ANToNyS21/DMP2025/prubezna kontrola/photos.docx

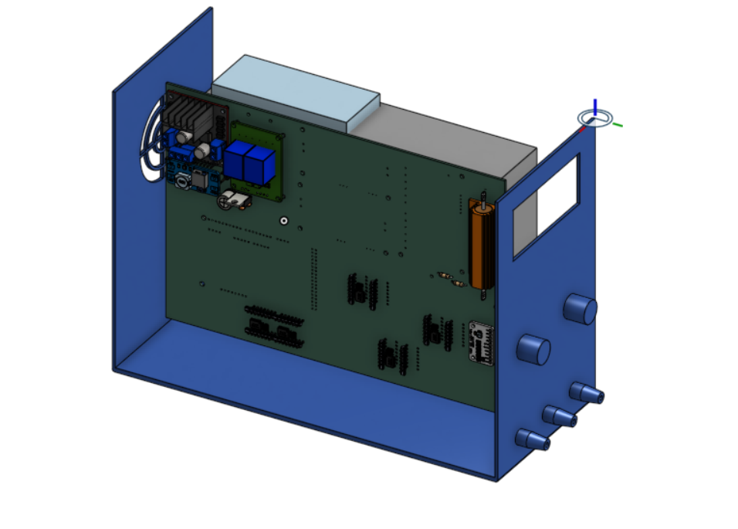
[picture p44: figure]
Obsah obrázku stroj/přístroj Popis byl vytvořen automaticky
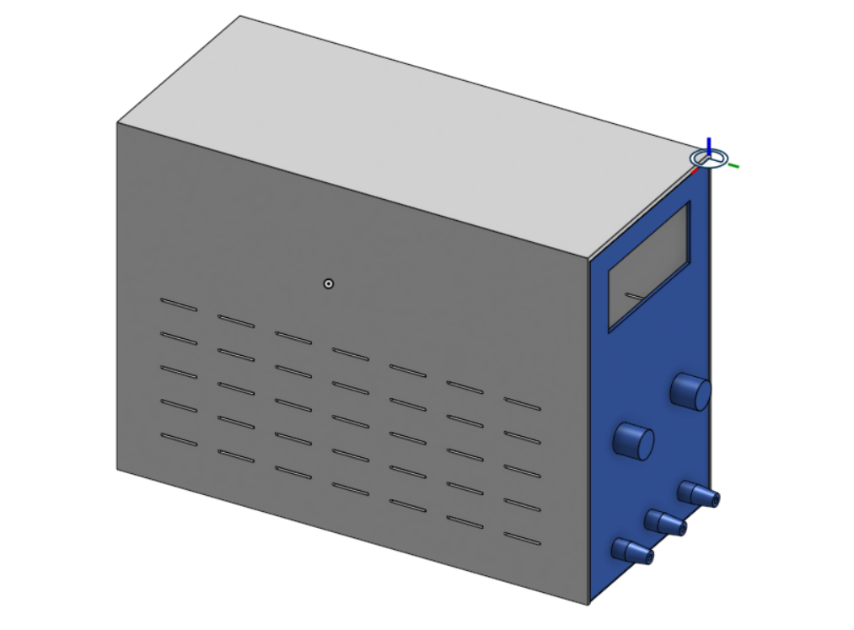
[picture p45: figure]
Obsah obrázku design Popis byl vytvořen automaticky
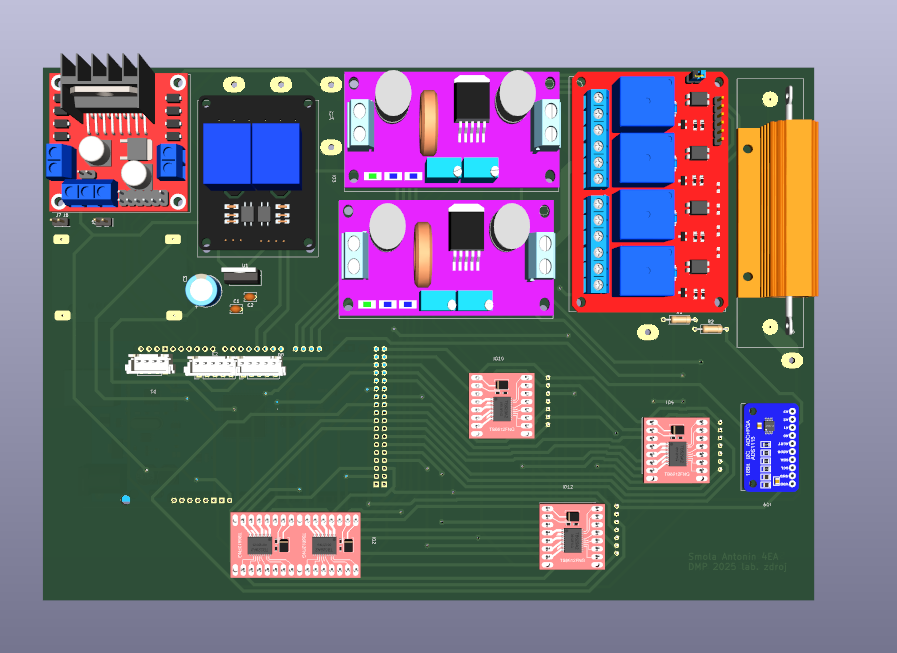
[picture p46: figure]
Obsah obrázku text, snímek obrazovky, Obdélník, Plán Popis byl vytvořen automaticky
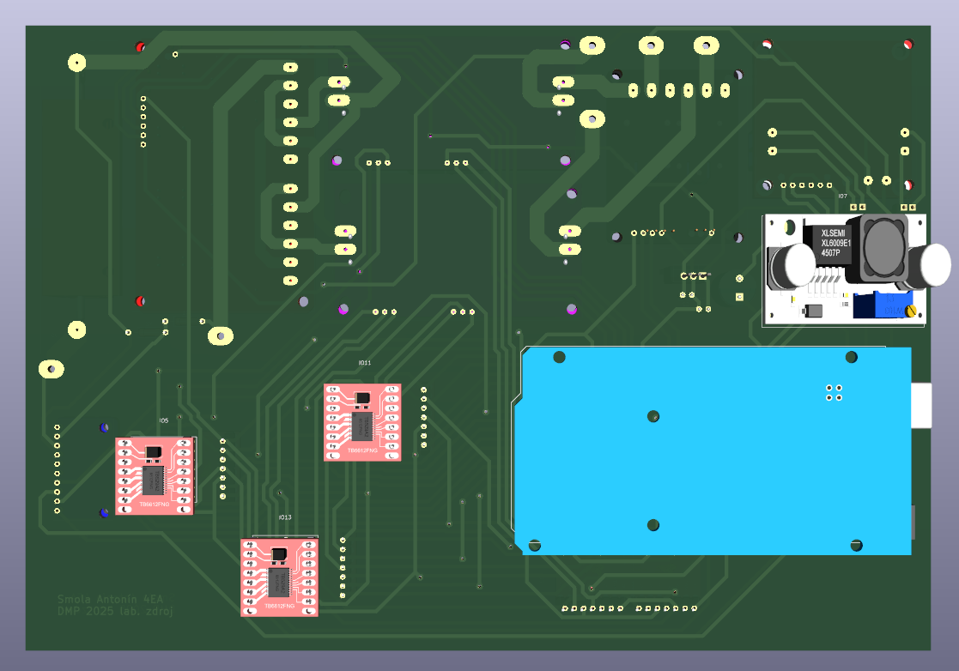
[picture p47: figure]
Obsah obrázku text, obvod, mapa, snímek obrazovky Popis byl vytvořen automaticky
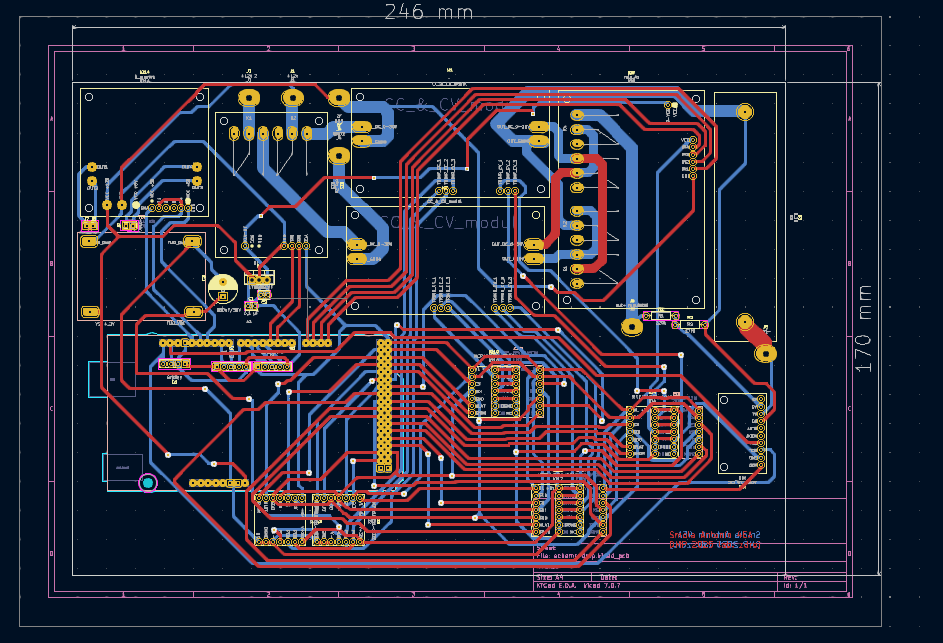
[picture p48: figure]
Obsah obrázku text, snímek obrazovky, obvod, mapa Popis byl vytvořen automaticky
