ANToNyS21/DMP2025/prubezna kontrola/prubezna prezentace.pptx

## Laboratorní zdroj

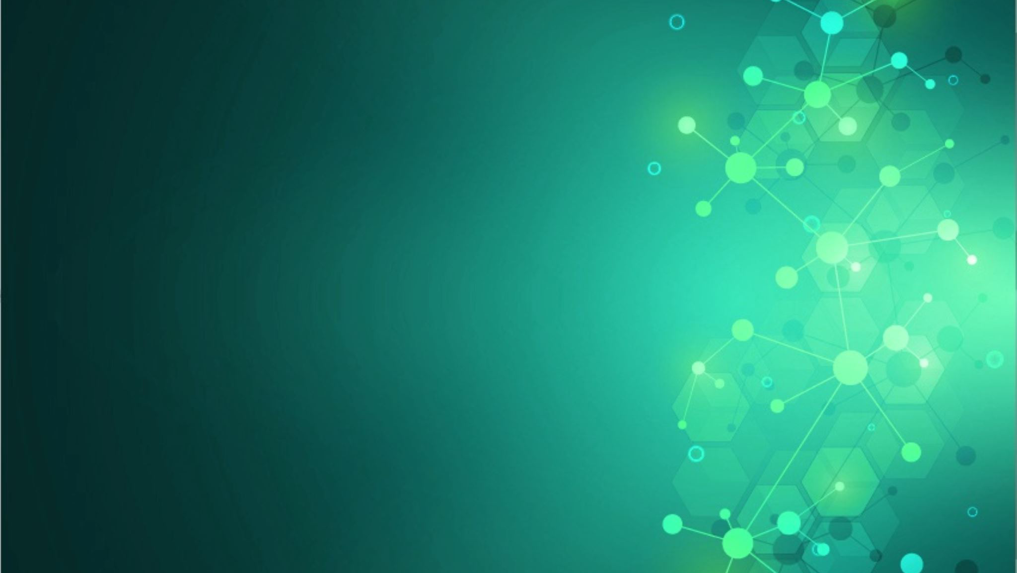
[picture p49: figure]
Obsah obrázku snímek obrazovky, voda, Tyrkysový, zelené Popis byl vytvořen automaticky

Smola Antonín 4EA
Vedoucí : Jan Kárník
05.11.2024

## Řešená témata:

Motivace
Problémy
Řešení
Momentální fáze

## Motivace

- Doplnění stávajícího analogového Laboratorního zdroje o digitální variantu
- Potřeba Laboratorního zdroje s enkoderem

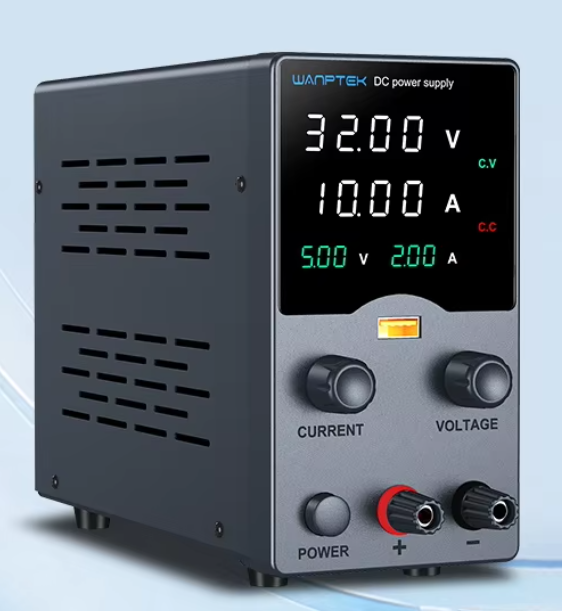
[picture p50: figure]

## Zakoupeno

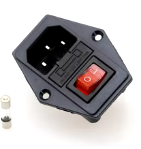
[picture p51: figure]
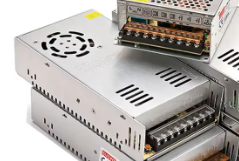
[picture p52: figure]
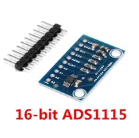
[picture p53: figure]
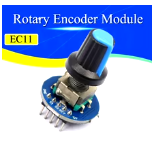
[picture p54: figure]
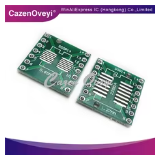
[picture p55: figure]
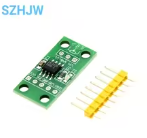
[picture p56: figure]
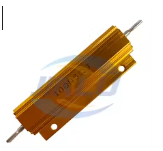
[picture p57: figure]
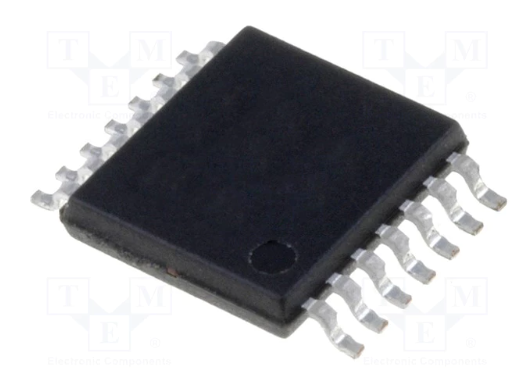
[picture p58: figure]
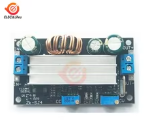
[picture p59: figure]

## Uděláno

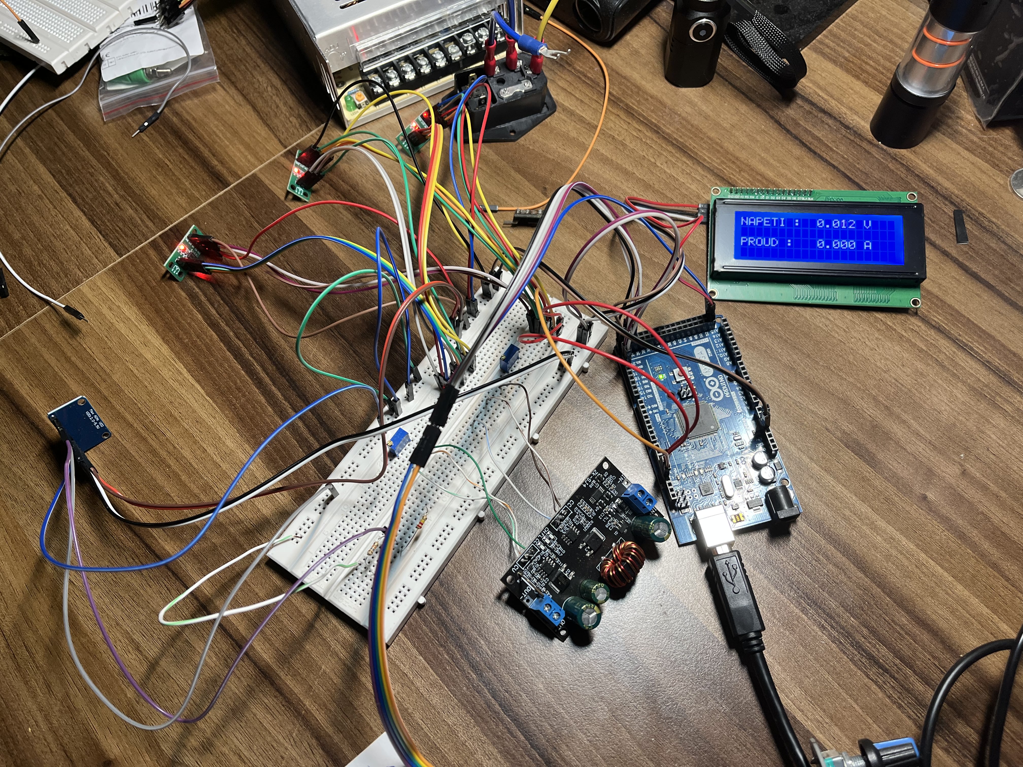
[picture p60: figure]
Obsah obrázku elektronika, Elektronické inženýrství, Elektrické vedení, kabel Popis byl vytvořen automaticky

## Uděláno

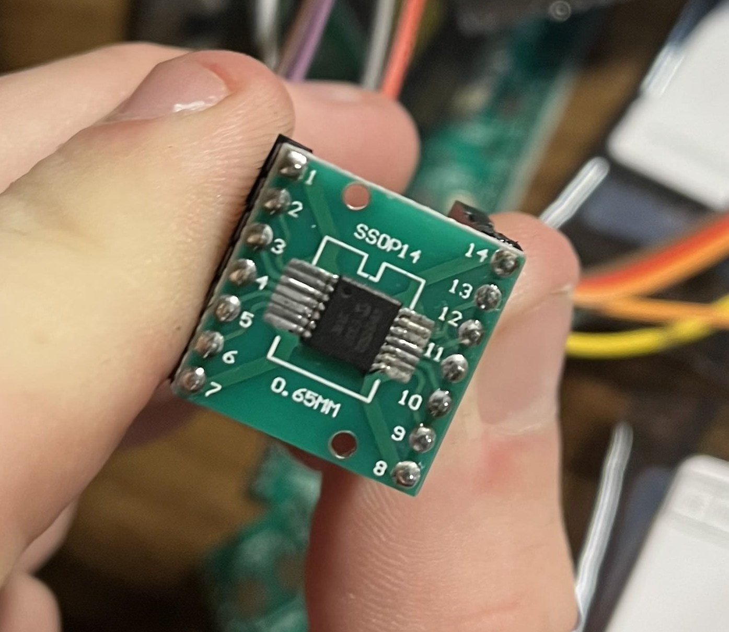
[picture p61: figure]
Obsah obrázku Elektronické inženýrství, Elektronická součástka, Obvodoví součástka, obvod Popis byl vytvořen automaticky

## Uděláno

- Videa:

## Konec Laboratorní zdroj

Smola Antonín 4EA
Vedoucí : Jan Kárník
05.11.2024
