ANToNyS21/DMP2025/prubezna kontrola/DMP_ELEKTRO.drawio.png

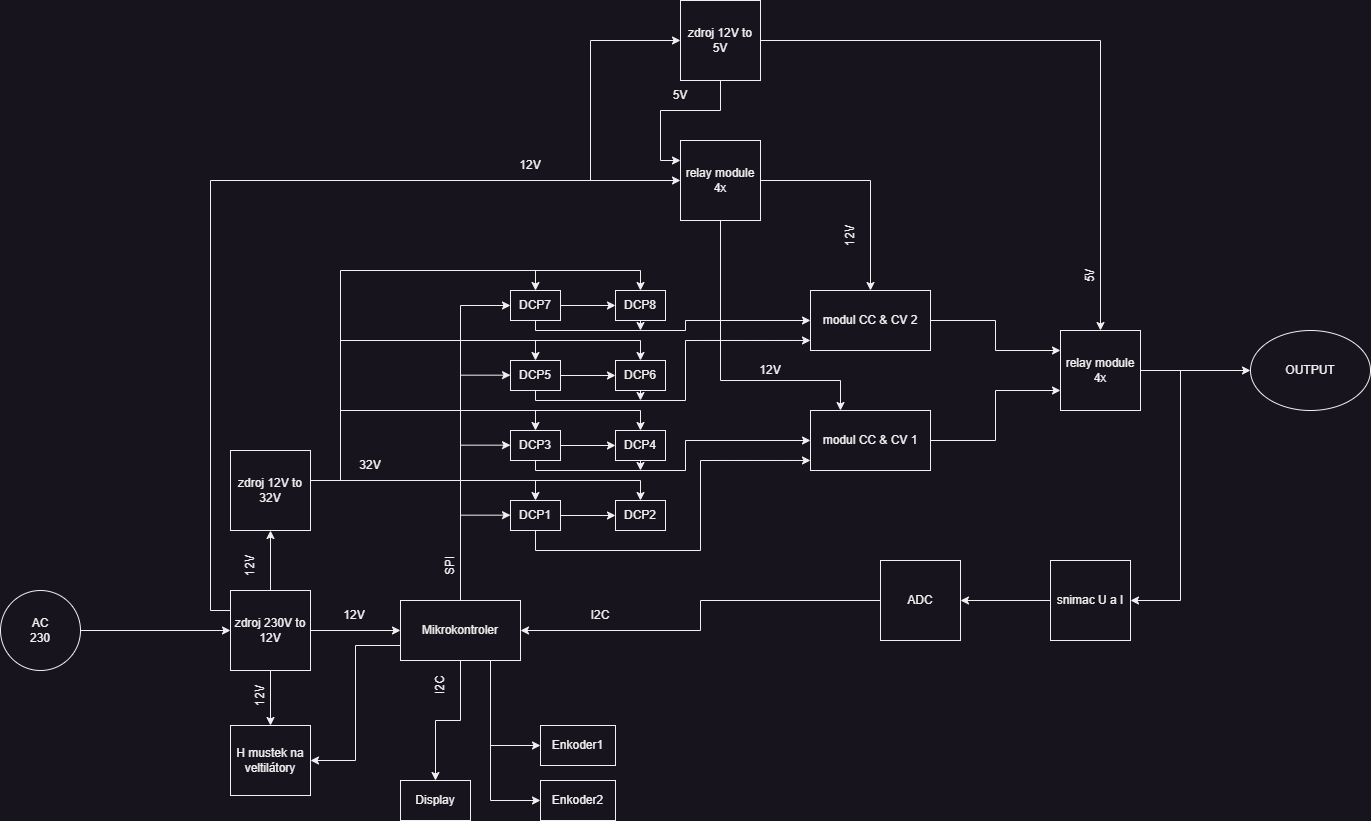
prubezna kontrola/DMP_ELEKTRO.drawio.png
