ANToNyS21/DMP2025/prubezna kontrola/program/prubezny diagram.png

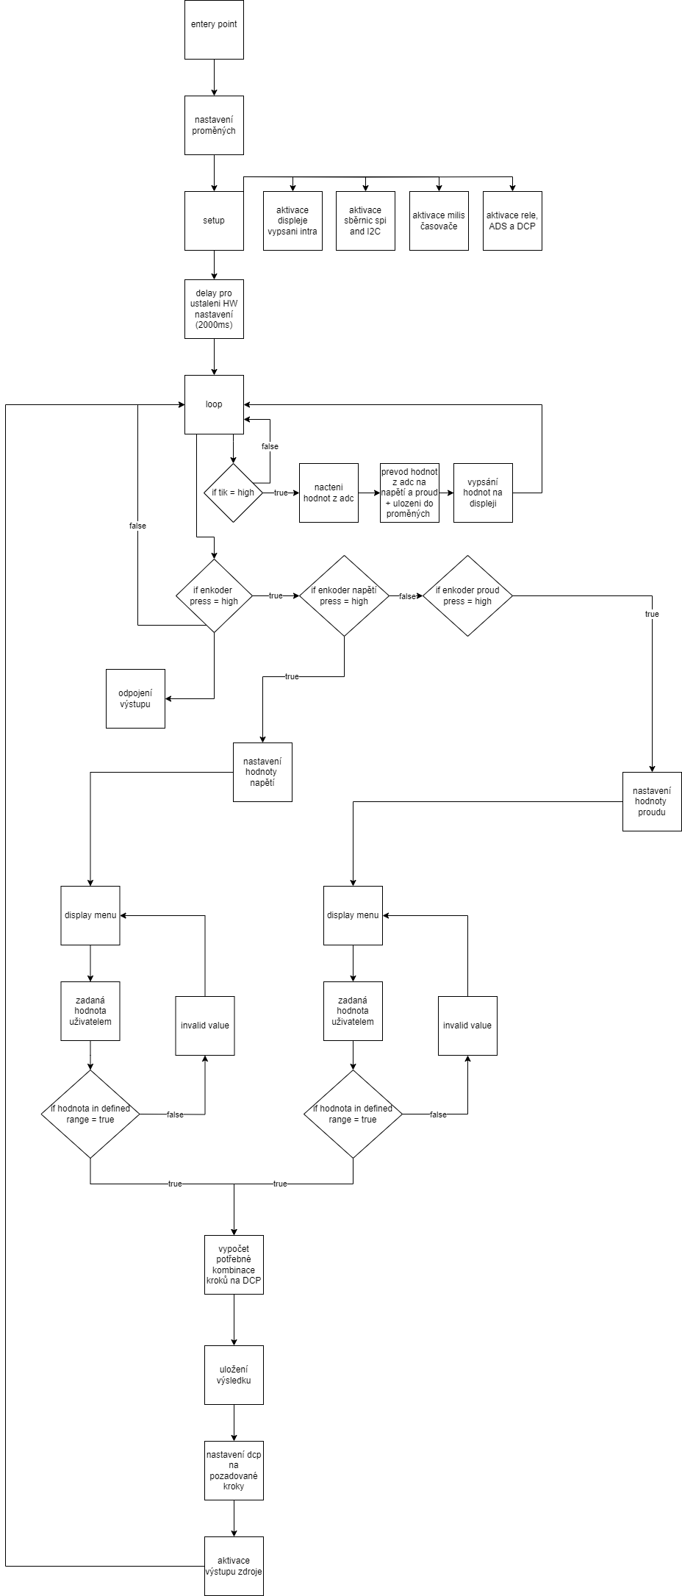
prubezna kontrola/program/prubezny diagram.png
