ANToNyS21/DMP2025/smolaan21/elektrika/board layout2.png

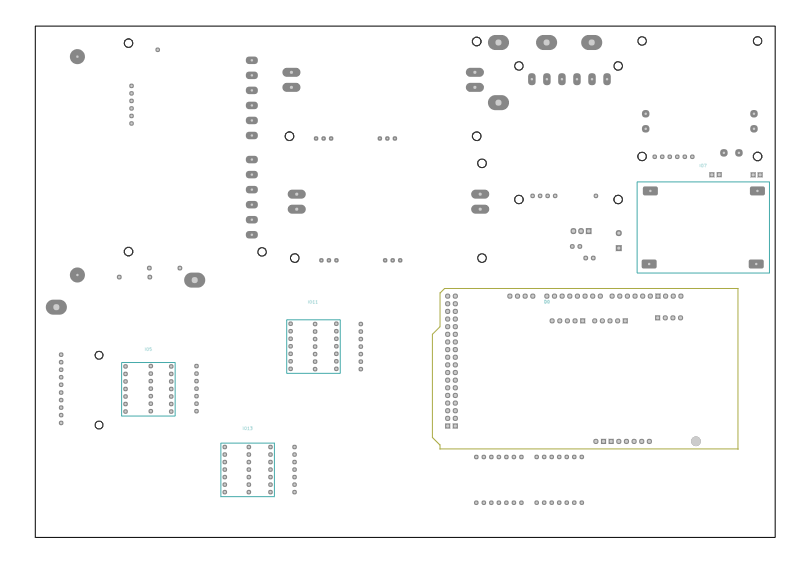
smolaan21/elektrika/board layout2.png
