ANToNyS21/DMP2025/smolaan21/elektrika/board layout.png

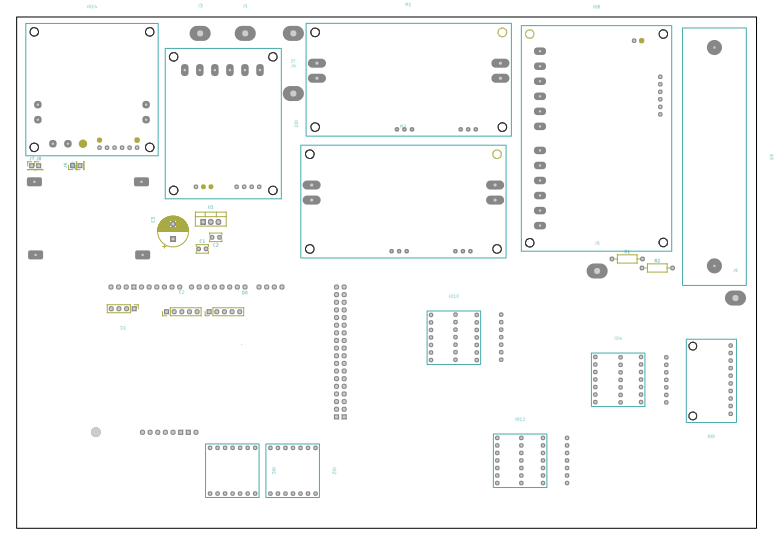
smolaan21/elektrika/board layout.png
