ANToNyS21/DMP2025/smolaan21/media/DCP_na_SMD_break_out.JPG

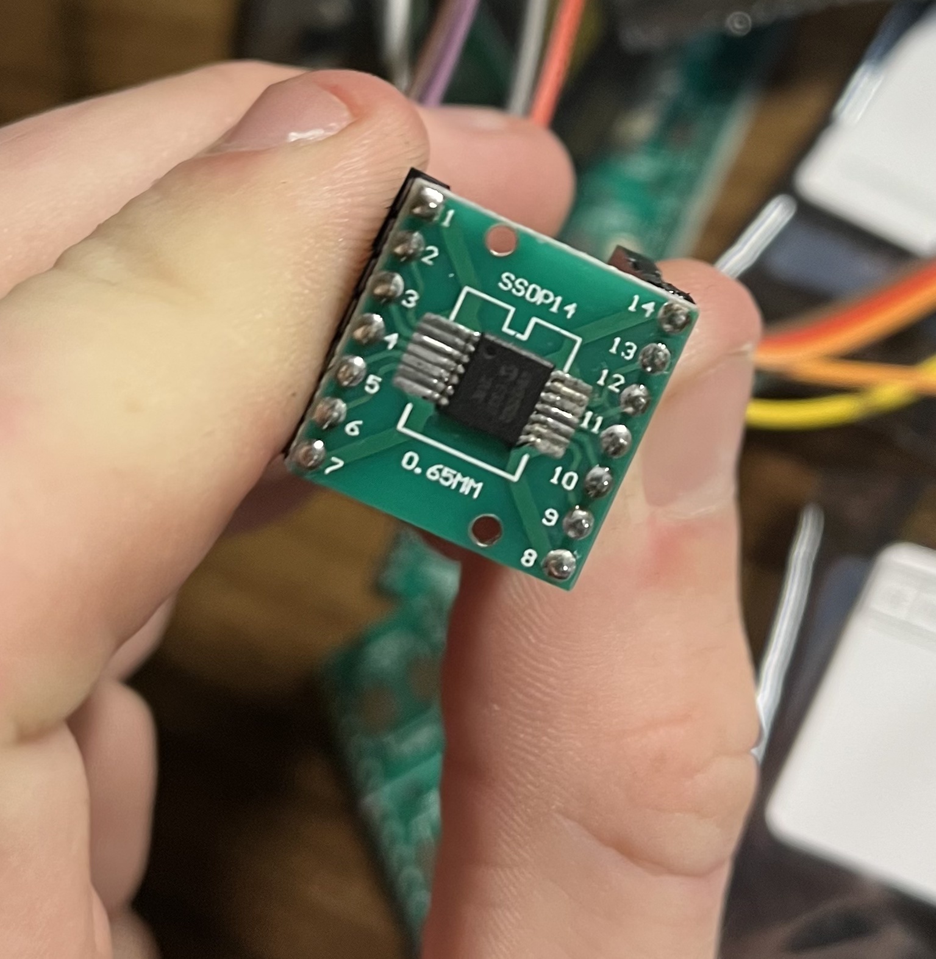
smolaan21/media/DCP_na_SMD_break_out.JPG
