ANToNyS21/DMP2025/smolaan21/media/DPS_s_arduinem.JPG

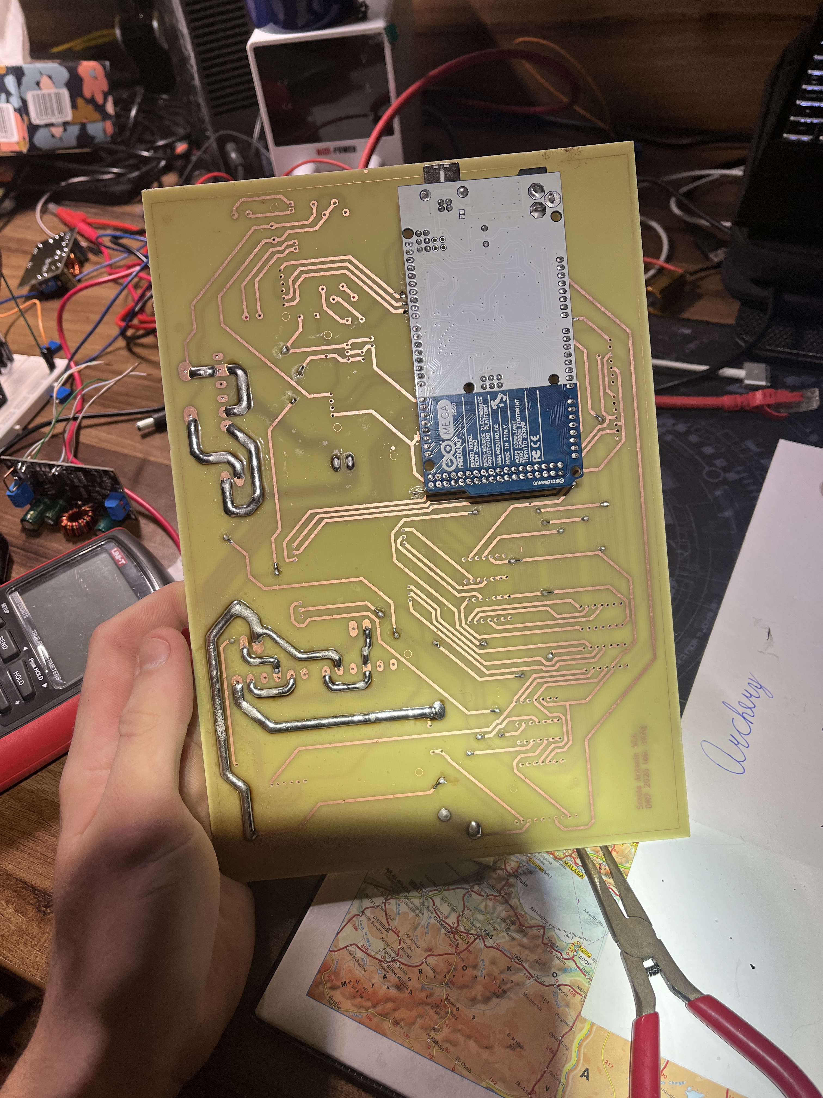
smolaan21/media/DPS_s_arduinem.JPG
