ANToNyS21/DMP2025/smolaan21/media/DPS_se_zesílenými_cestami.JPG

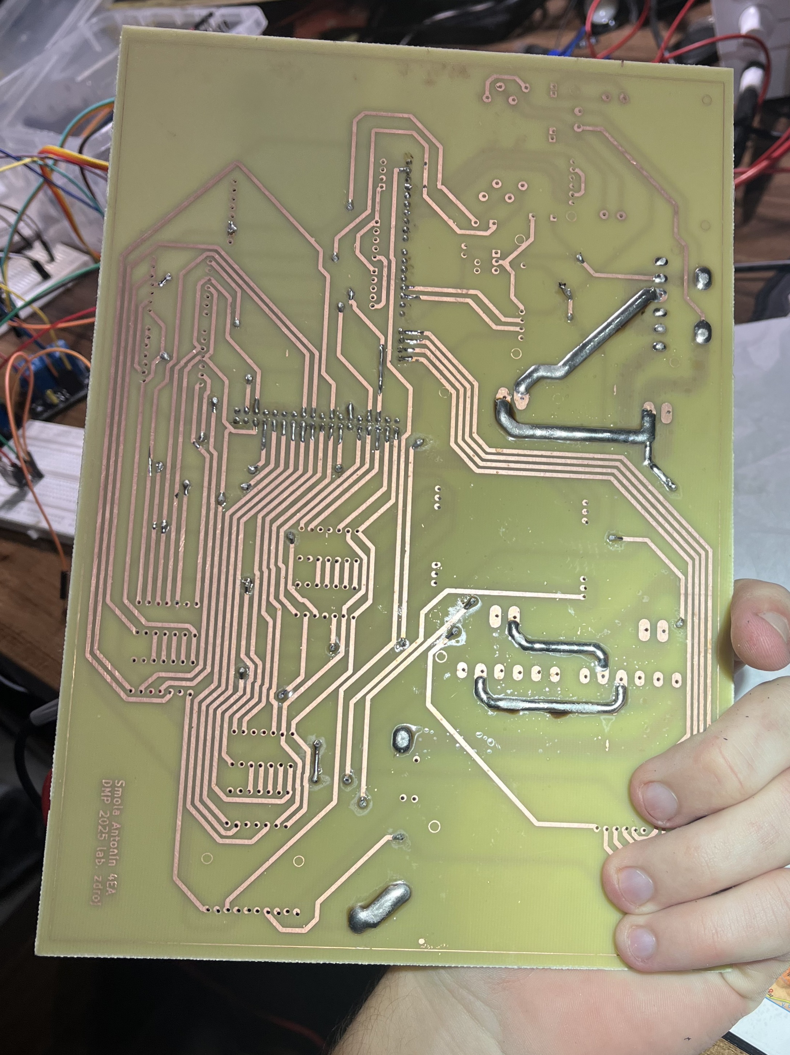
smolaan21/media/DPS_se_zesílenými_cestami.JPG
