ANToNyS21/DMP2025/smolaan21/media/finalně_osazená_DPS_B.jpg

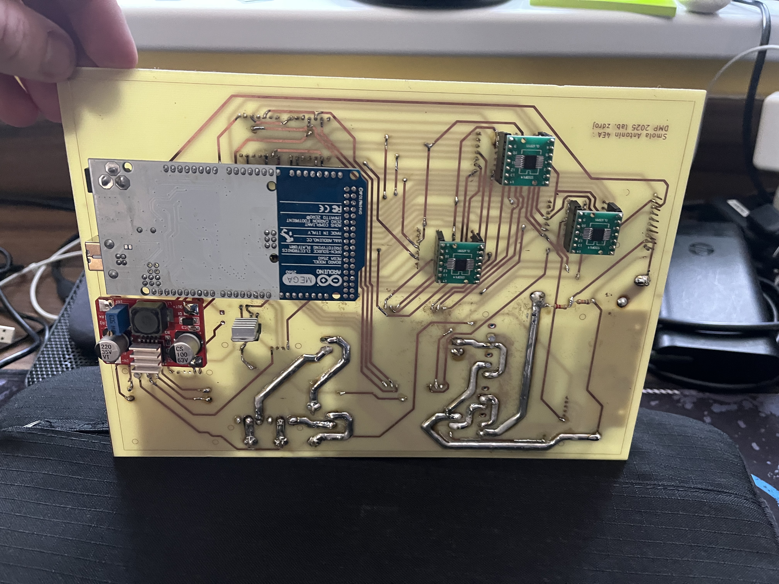
smolaan21/media/finalně_osazená_DPS_B.jpg
