ANToNyS21/DMP2025/smolaan21/media/finalně_osazená_DPS_F.jpg

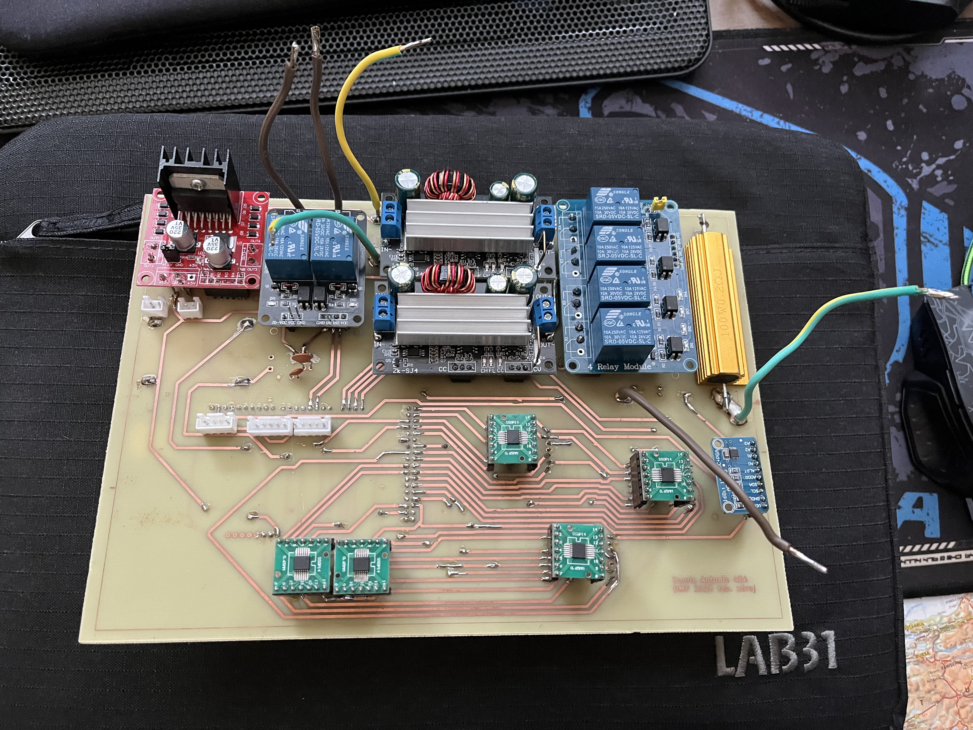
smolaan21/media/finalně_osazená_DPS_F.jpg
