ANToNyS21/DMP2025/smolaan21/media/finálně_osazená_schránka1.jpeg

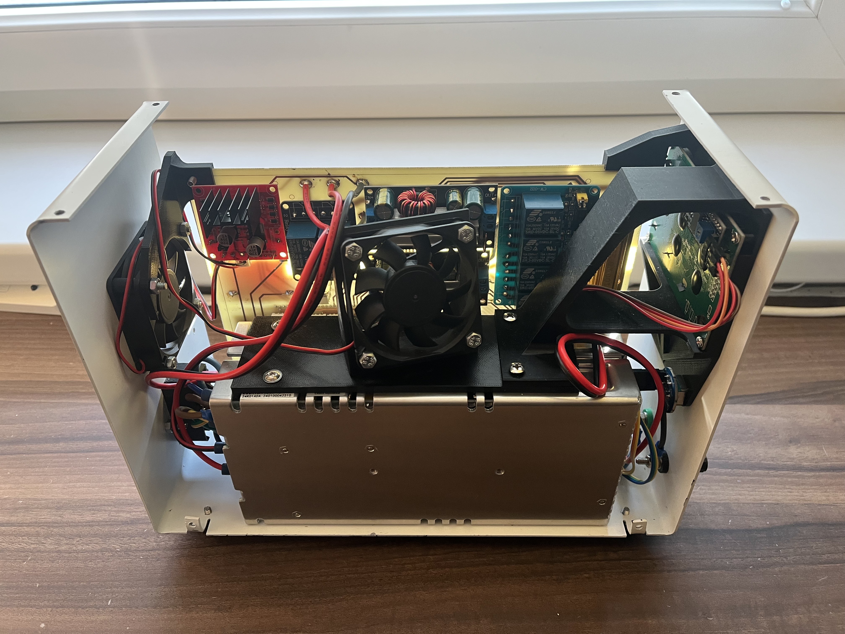
smolaan21/media/finálně_osazená_schránka1.jpeg
