ANToNyS21/DMP2025/smolaan21/media/nanesený_lak.jpeg

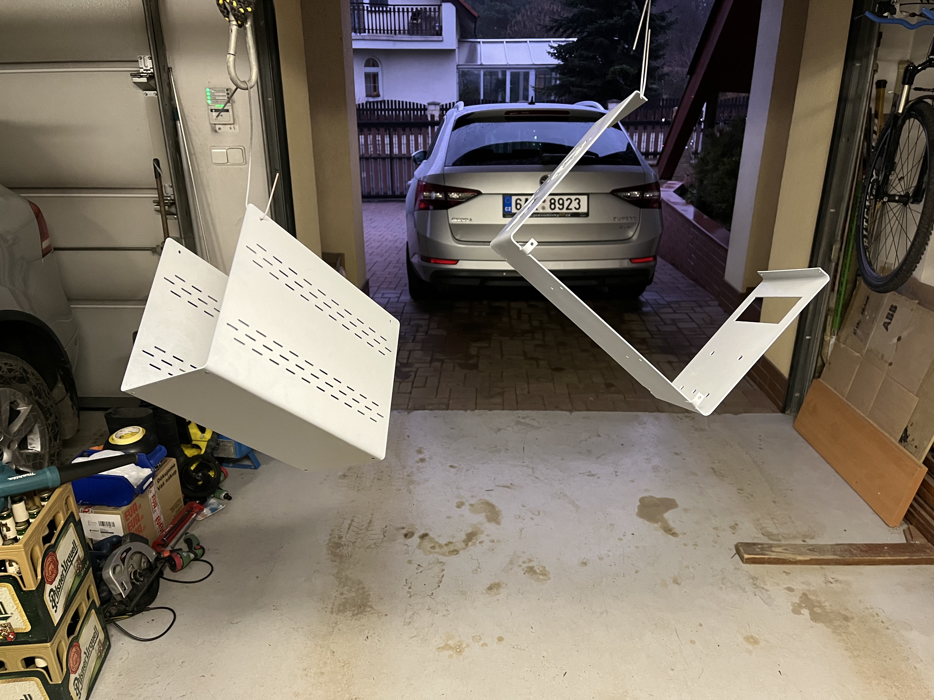
smolaan21/media/nanesený_lak.jpeg
