ANToNyS21/DMP2025/smolaan21/media/nanesený_plnič.jpeg

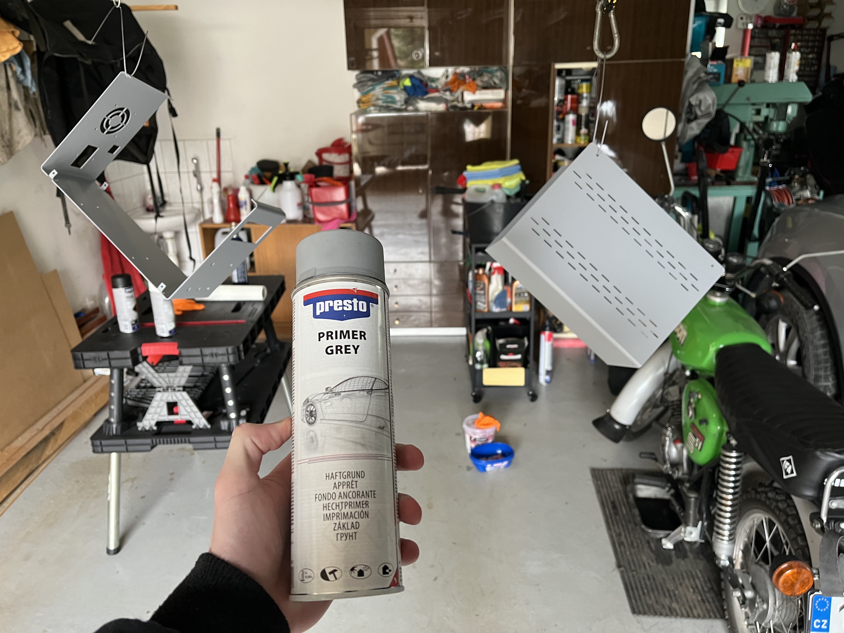
smolaan21/media/nanesený_plnič.jpeg
