ANToNyS21/DMP2025/smolaan21/media/naohýbaná_schránka2.jpeg

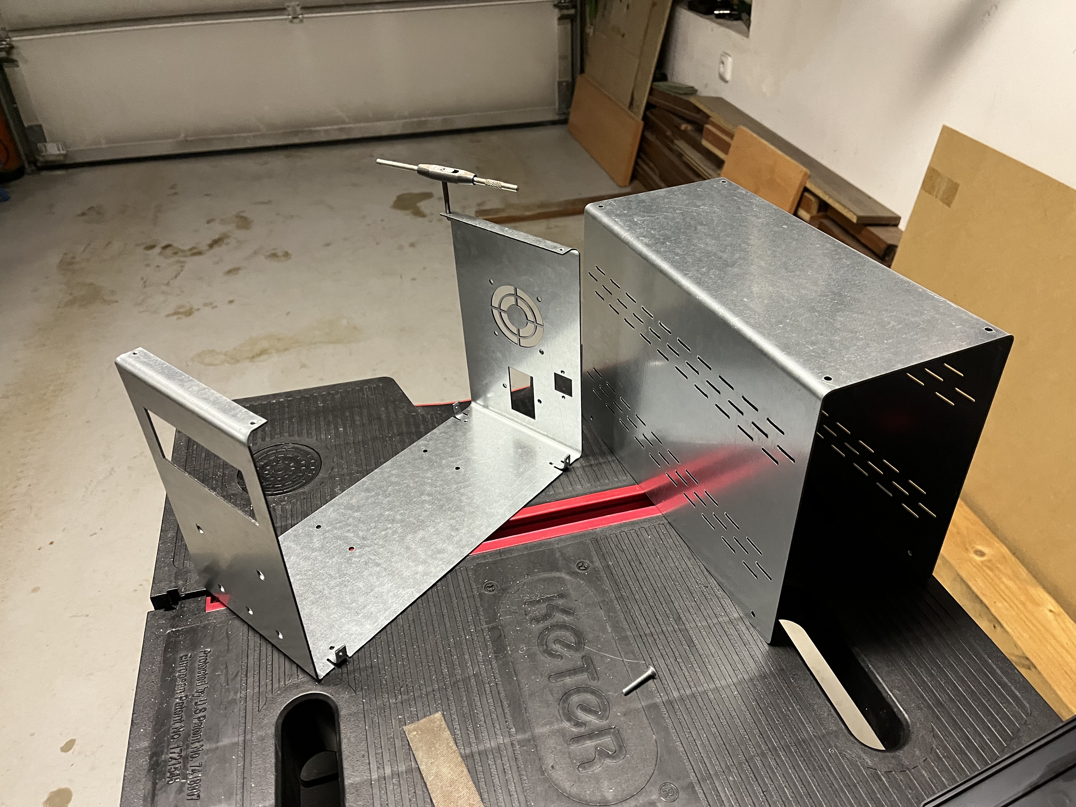
smolaan21/media/naohýbaná_schránka2.jpeg
