ANToNyS21/DMP2025/smolaan21/media/naohýbaná_schránka4.jpeg

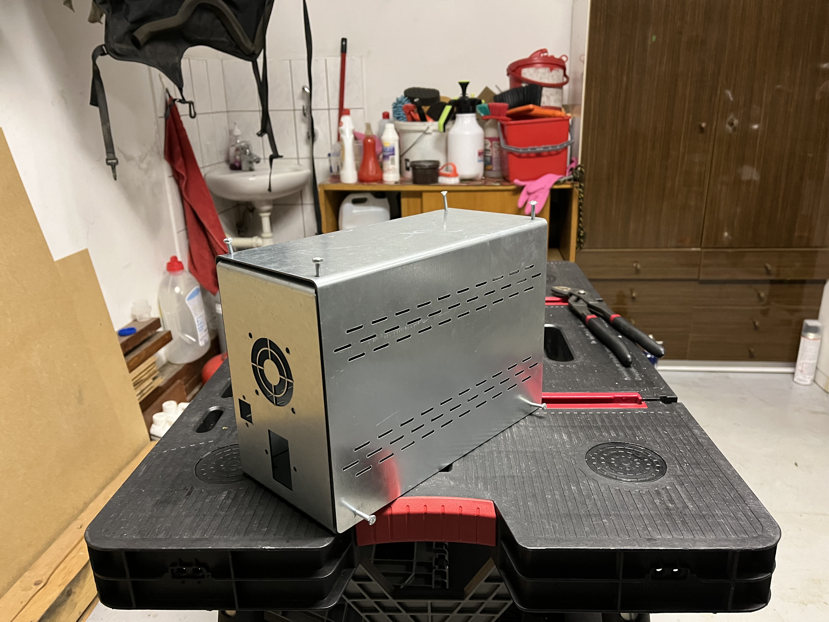
smolaan21/media/naohýbaná_schránka4.jpeg
