ANToNyS21/DMP2025/smolaan21/media/připojené_konektory_UI.jpg

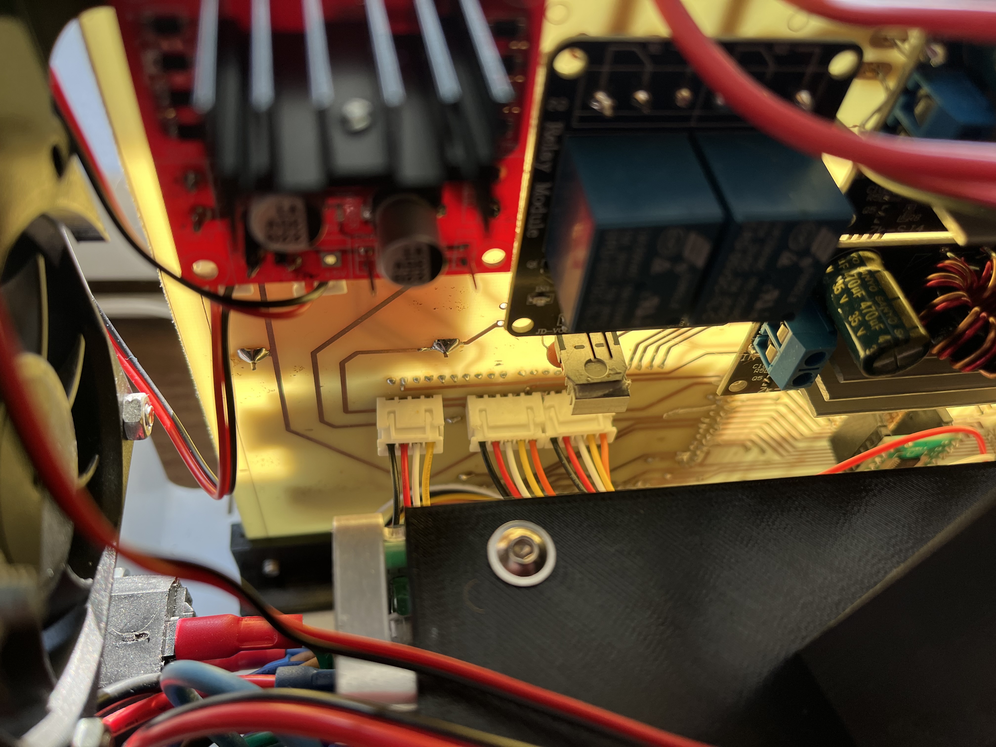
smolaan21/media/připojené_konektory_UI.jpg
