ANToNyS21/DMP2025/smolaan21/media/zakrytovaný_laboratorní_zdroj_s_polepy_2.jpg

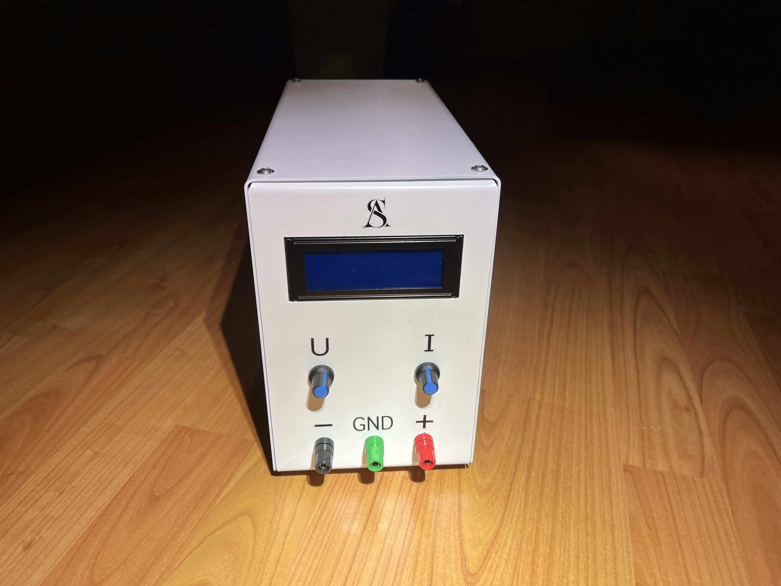
smolaan21/media/zakrytovaný_laboratorní_zdroj_s_polepy_2.jpg
