ANToNyS21/DMP2025/smolaan21/media/školní_leptací_stanice.jpg

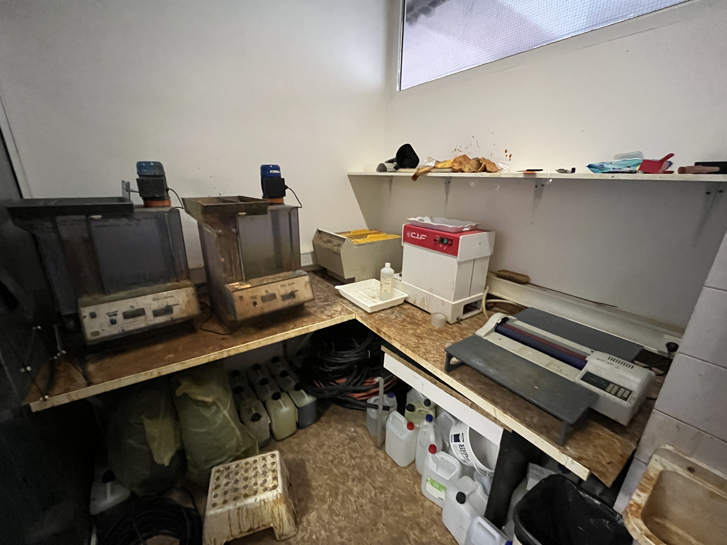
smolaan21/media/školní_leptací_stanice.jpg
