ANToNyS21/DMP2025/knihovna_kicad/Smola_dmp/100W 30OHM RESISTOR.STEP

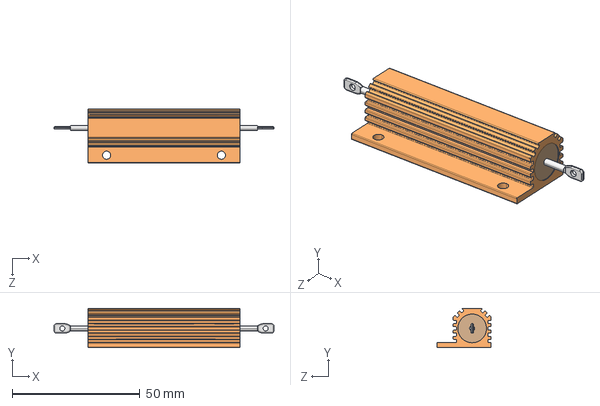
[picture p102: CAD file, 2025-02-05]
knihovna_kicad/Smola_dmp/100W 30OHM RESISTOR.STEP
86.2 x 15.4 x 21.2 mm
