ANToNyS21/DMP2025/smolaan21/mechanika/sheetmetal 1.5mm - programing port cap.step

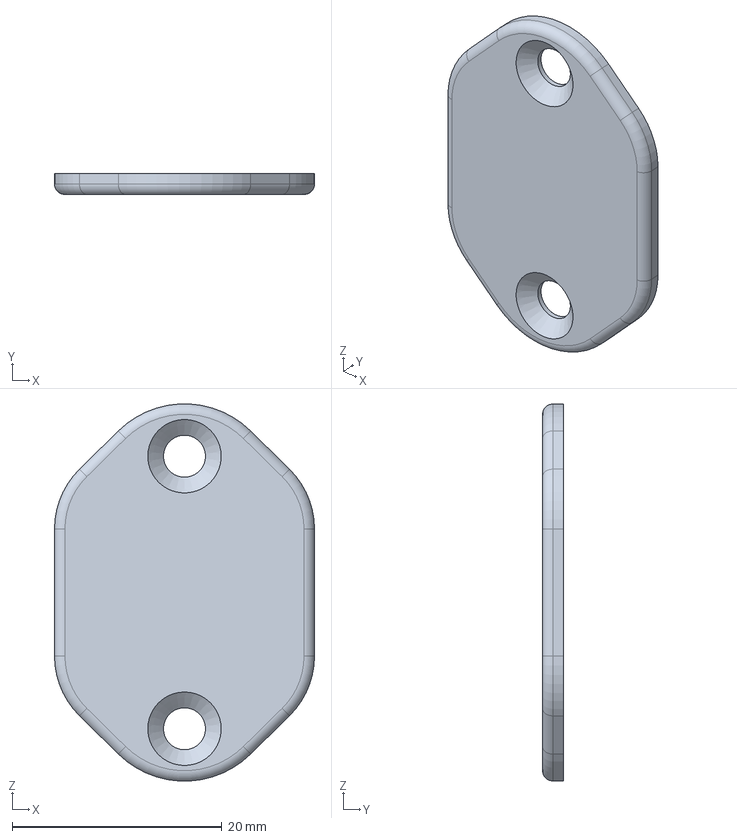
[picture p103: CAD file, 2025-02-25]
smolaan21/mechanika/sheetmetal 1.5mm - programing port cap.step
24.8 x 2.00 x 36.0 mm
