ANToNyS21/DMP2025/smolaan21/mechanika/stencil_front.step

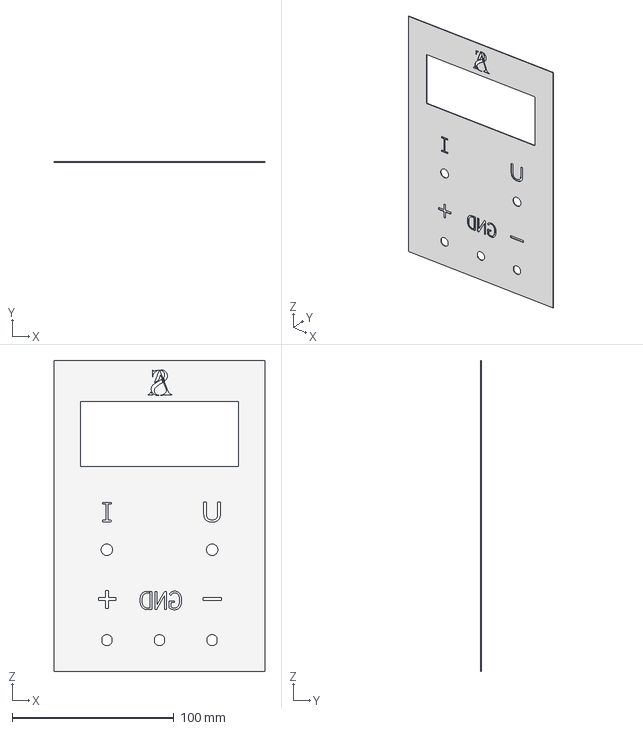
[picture p104: CAD file, 2025-02-25]
smolaan21/mechanika/stencil_front.step
130.0 x 0.5 x 192.0 mm
