ANToNyS21/DMP2025/schema dmp/schema dmp.pdf

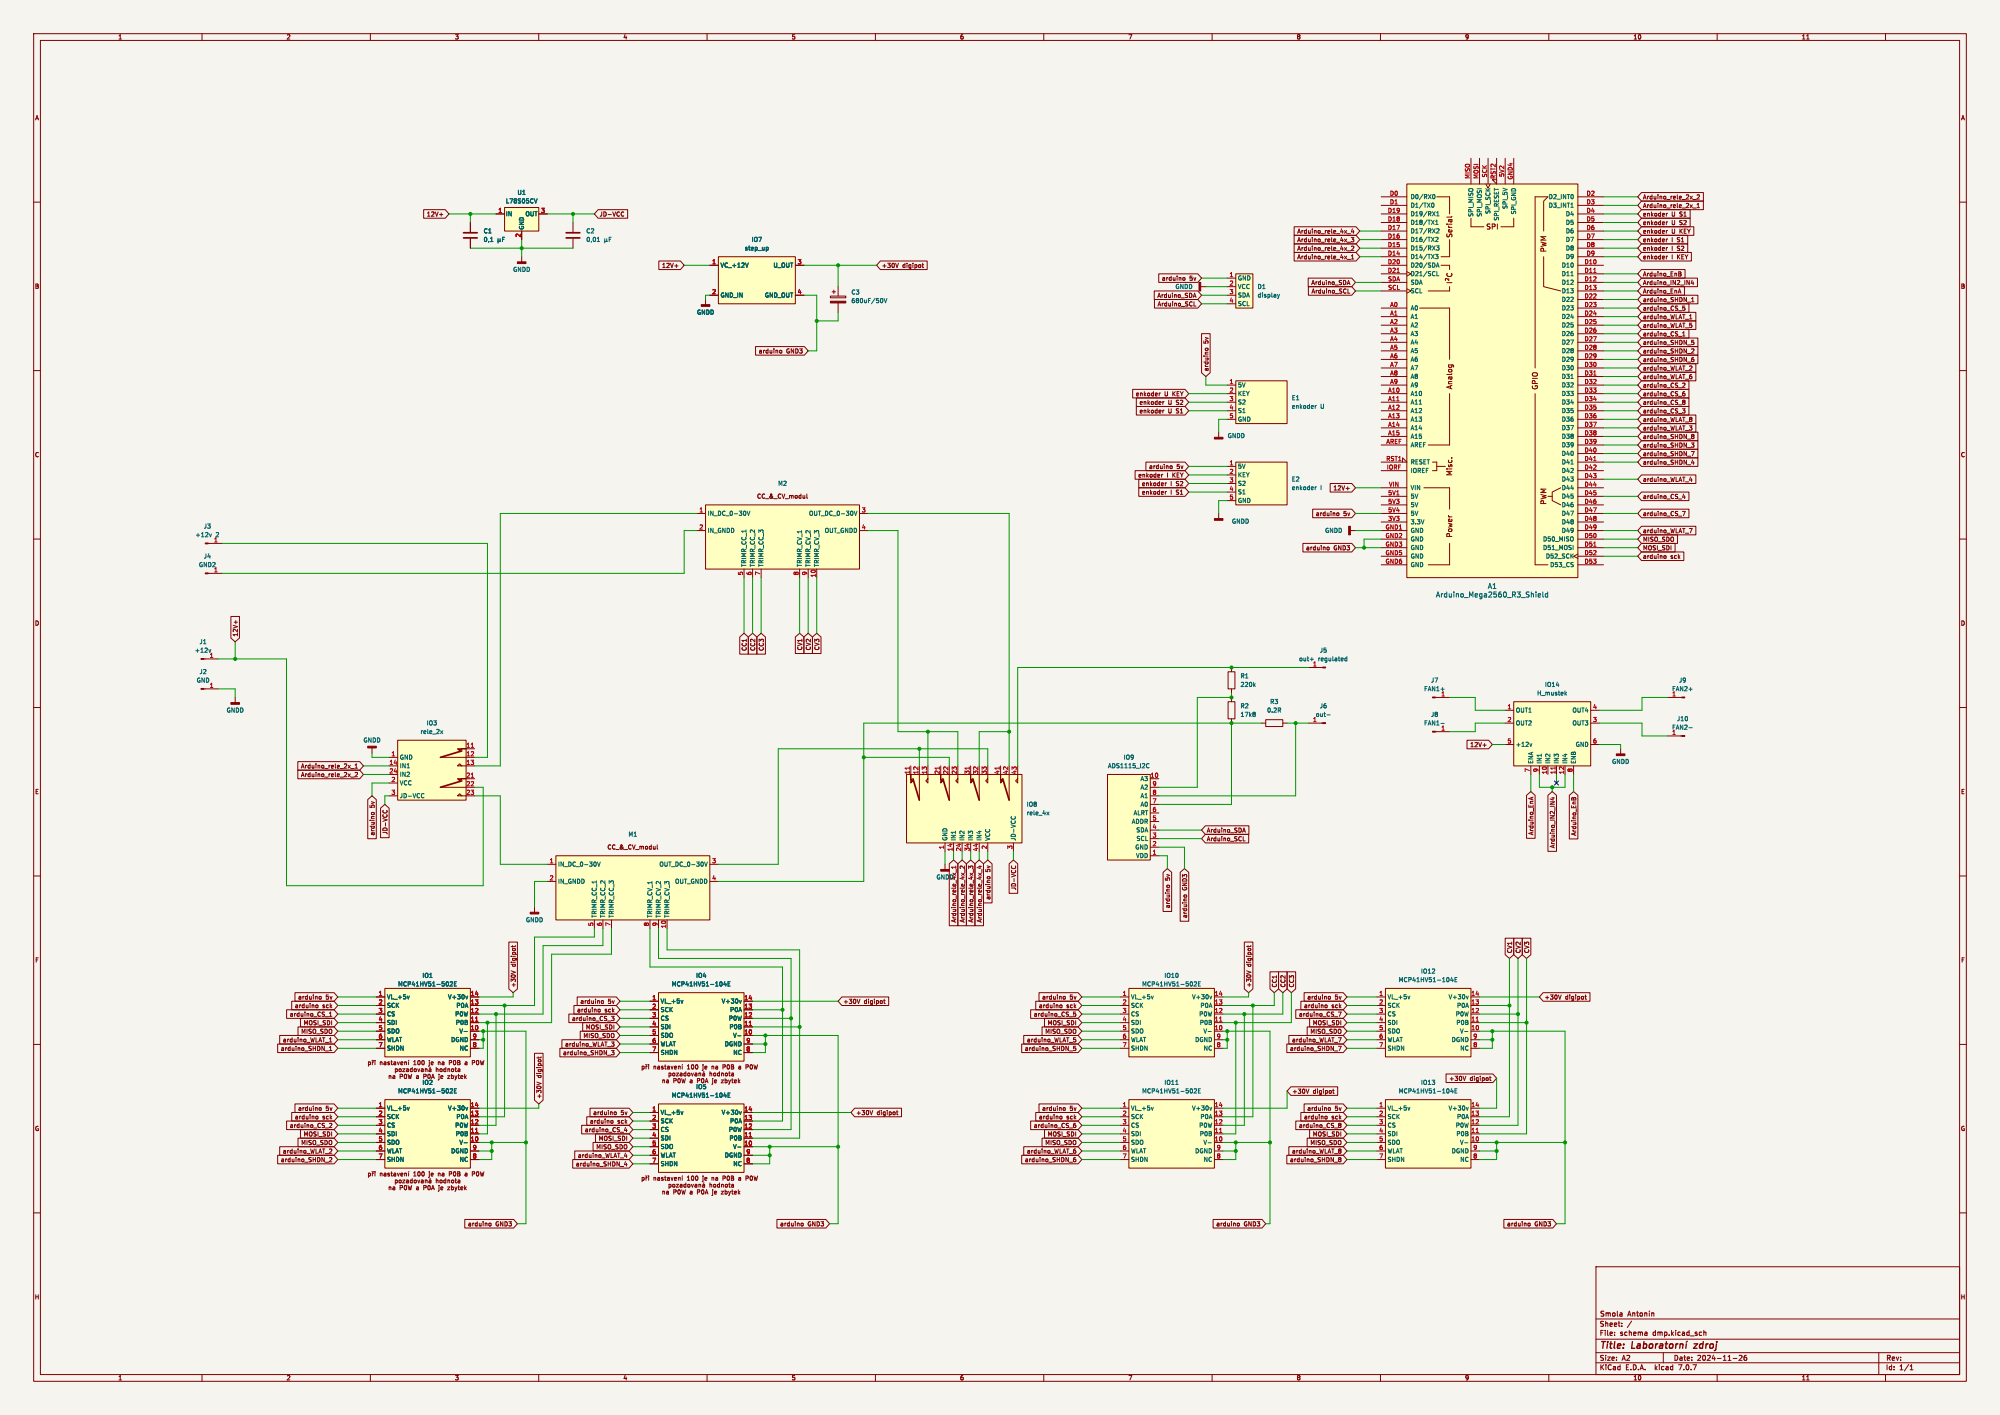
[picture p105: page 1]

VDD 1 A3 10 GND 2 SCL 3 SDA 4 ADDR 5 ALRT 6 A0 7 A1 8 A2 9

þÿpYi þÿnastavení 100 je na P0B a P0W þÿpozadovaná hodnota
