ANToNyS21/DMP2025/smolaan21/elektrika/schema dmp.pdf

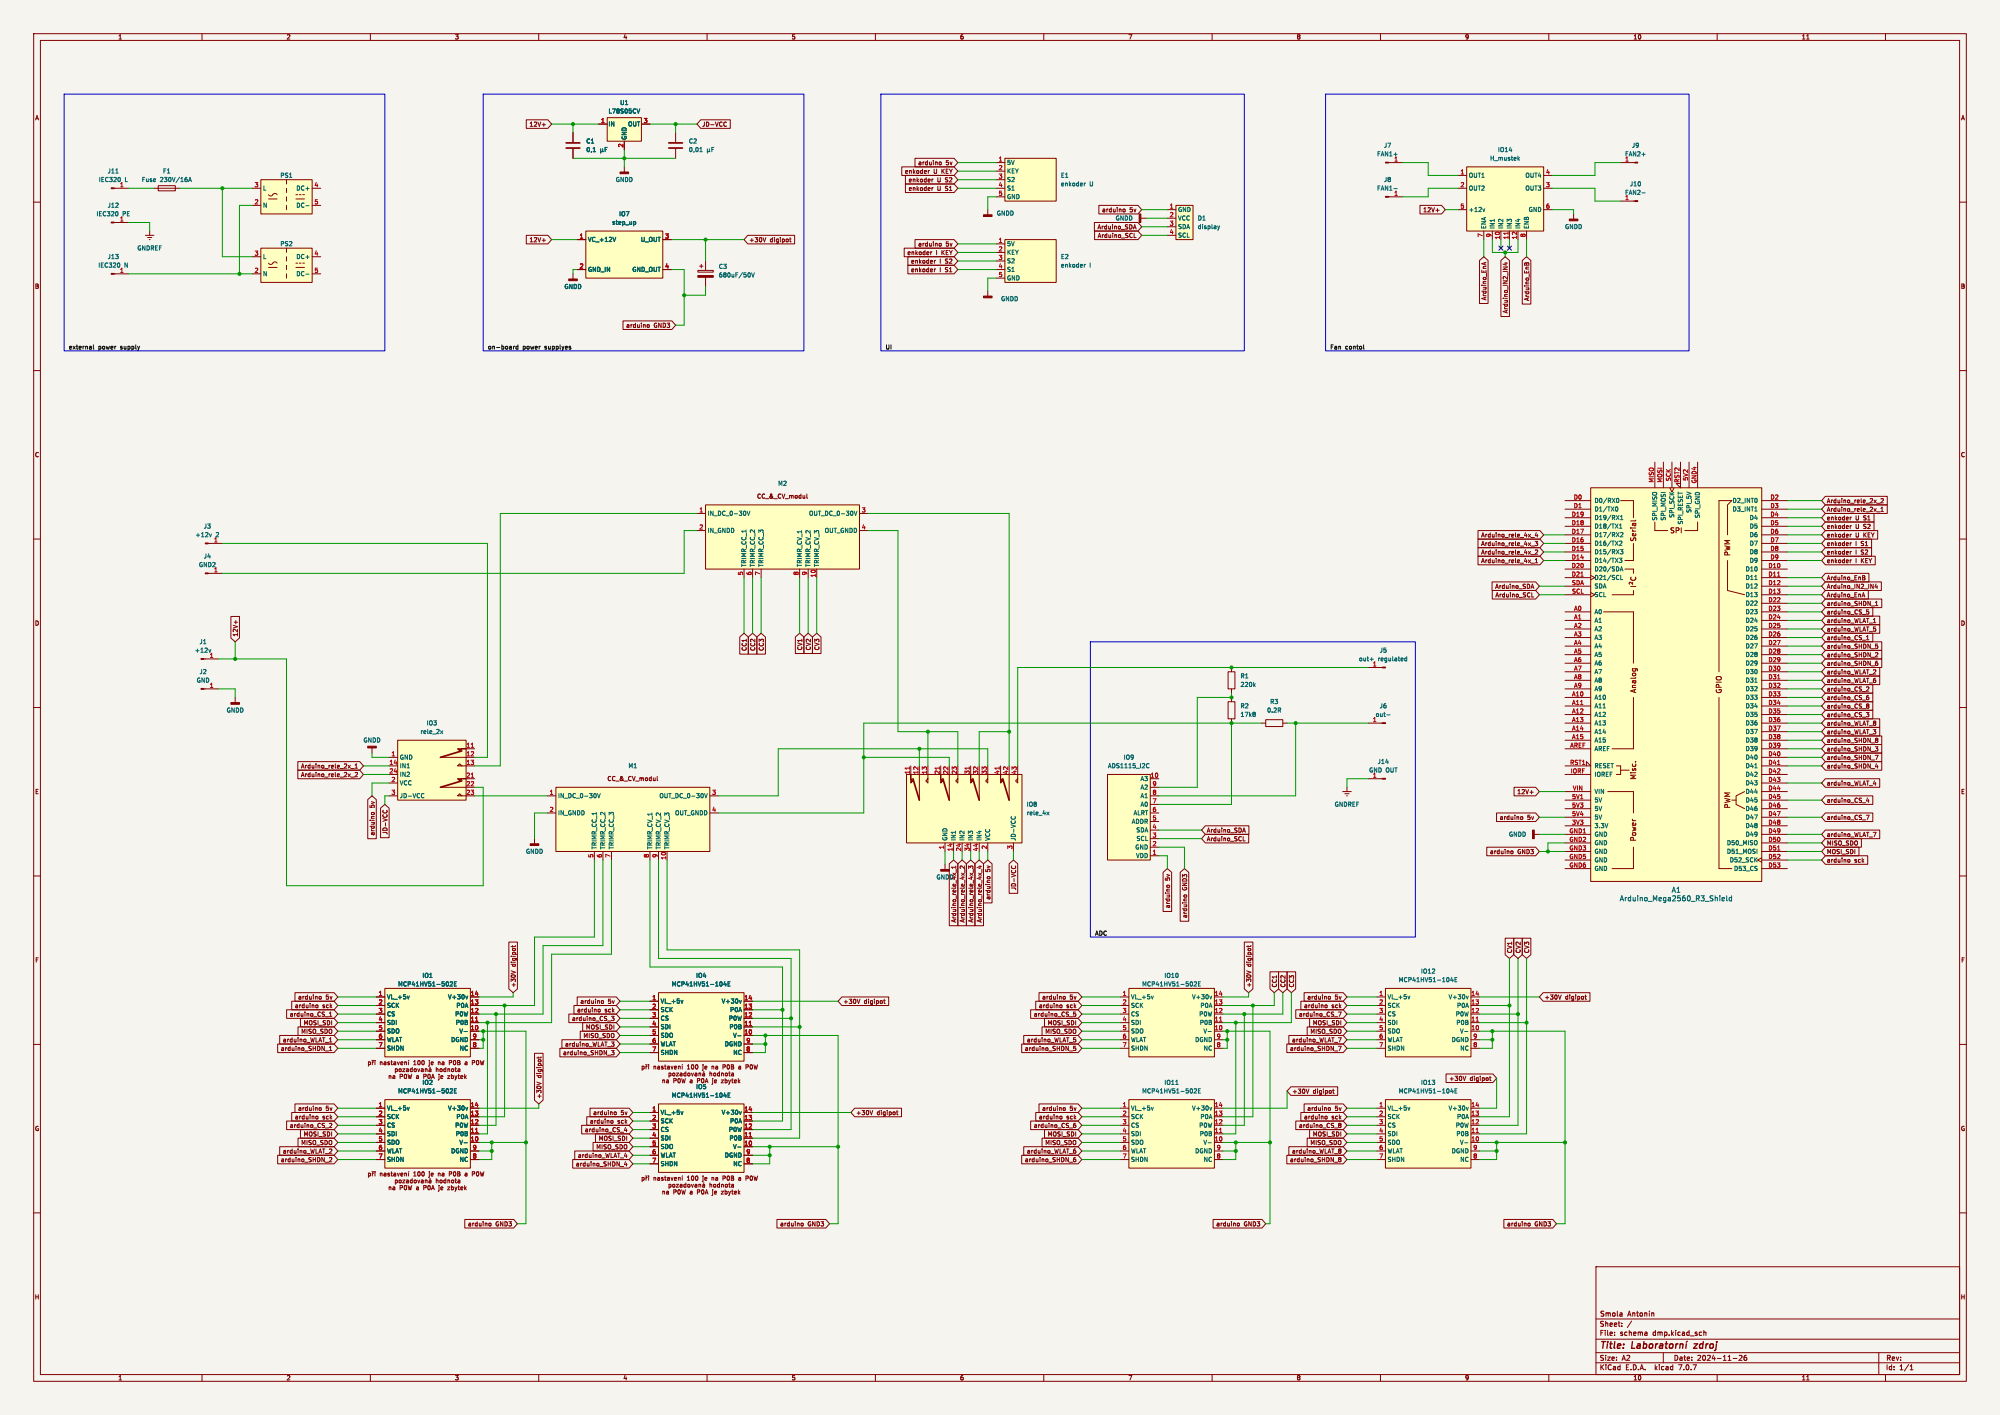
[picture p106: page 1]

9 M2 GND 1 VCC 2 SDA 3 SCL 4 D1

arduino sck arduino sck arduino 5v arduino_CS_3 +30V digipot

þÿpYi þÿnastavení 100 je na P0B a P0W þÿpozadovaná hodnota
