ANToNyS21/DMP2025/schema dmp/schema dmp nahled.pdf

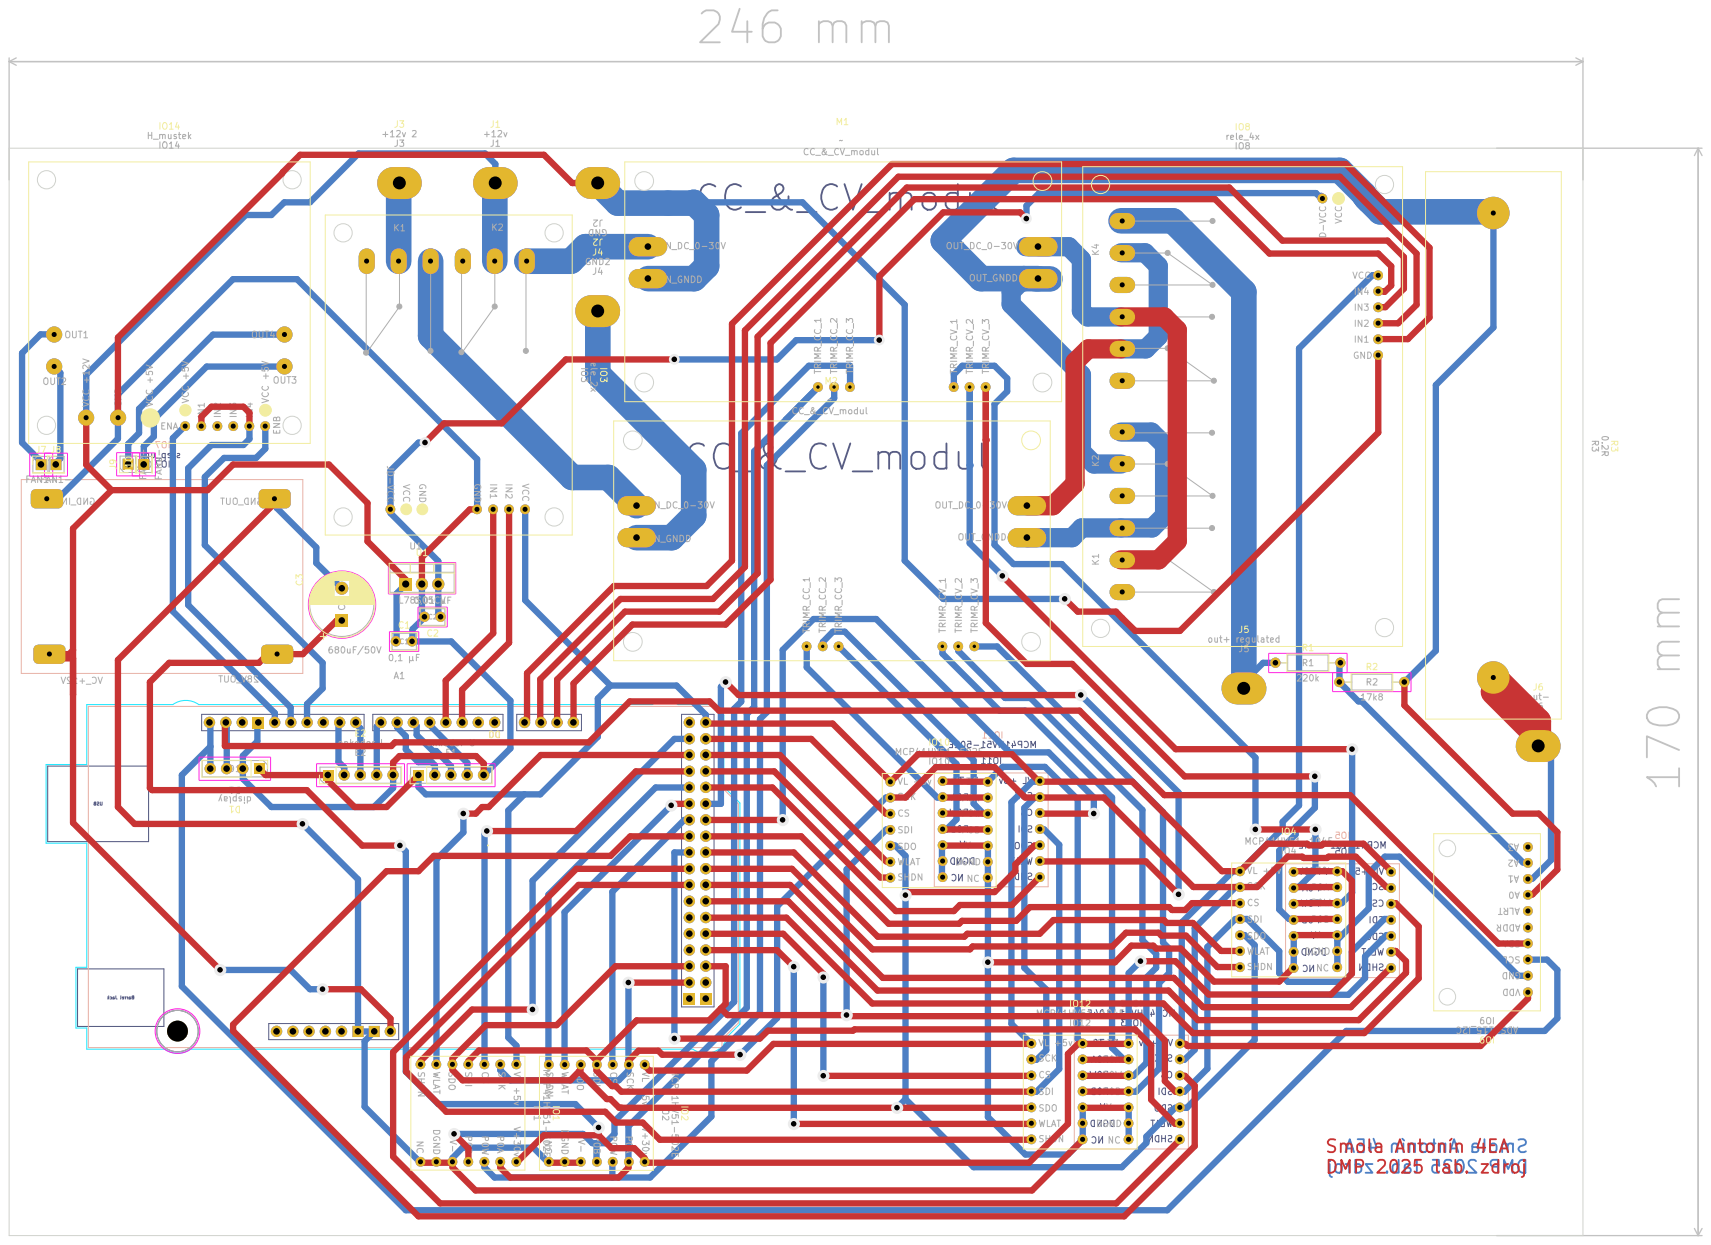
[picture p107: page 1]
