ANToNyS21/DMP2025/schema dmp/schema dmp-B_Cu.pdf

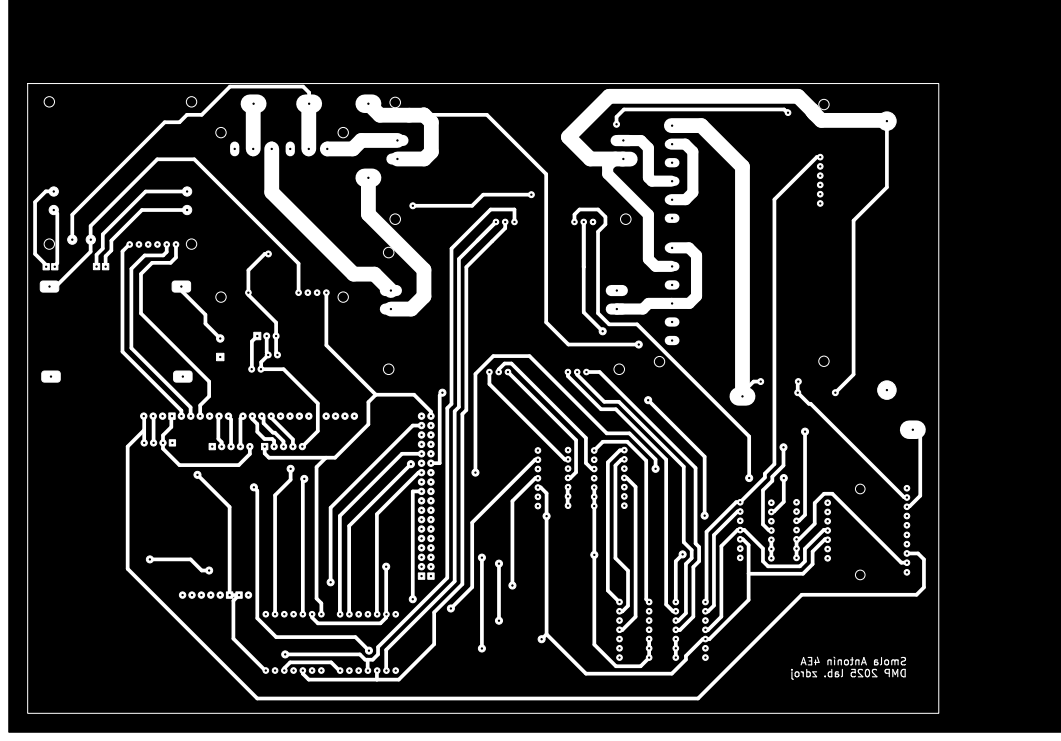
[picture p108: page 1]
