ANToNyS21/DMP2025/schema dmp/schema dmp-F_Cu.pdf

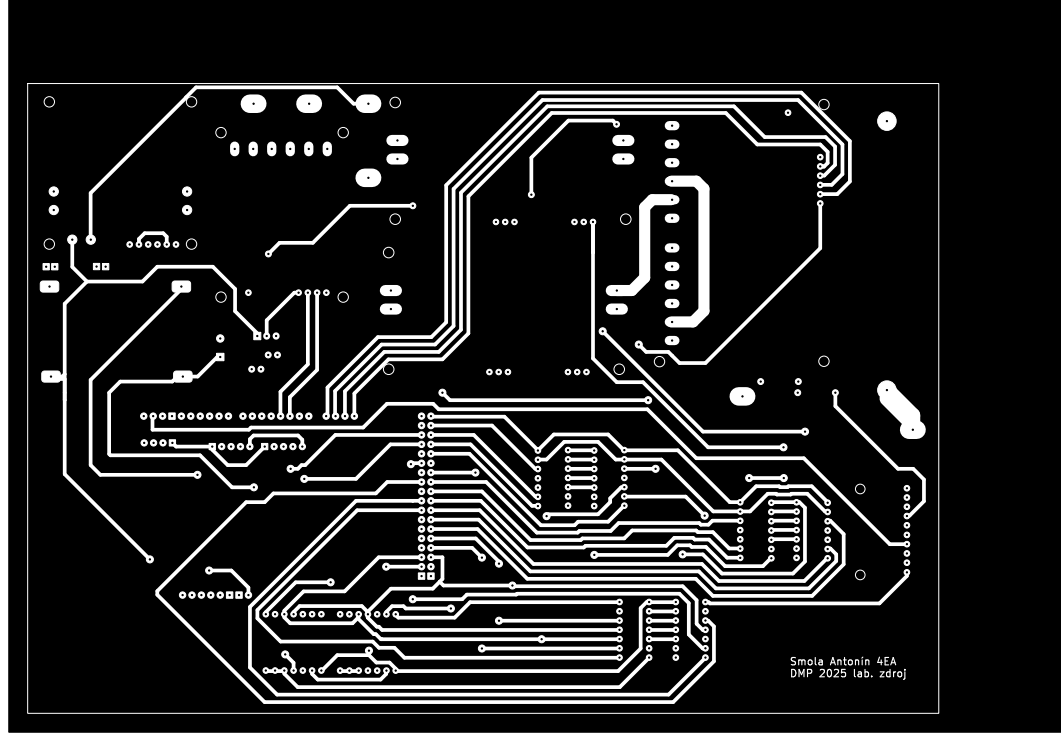
[picture p109: page 1]
