ANToNyS21/DMP2025/smolaan21/elektrika/dmp board.pdf

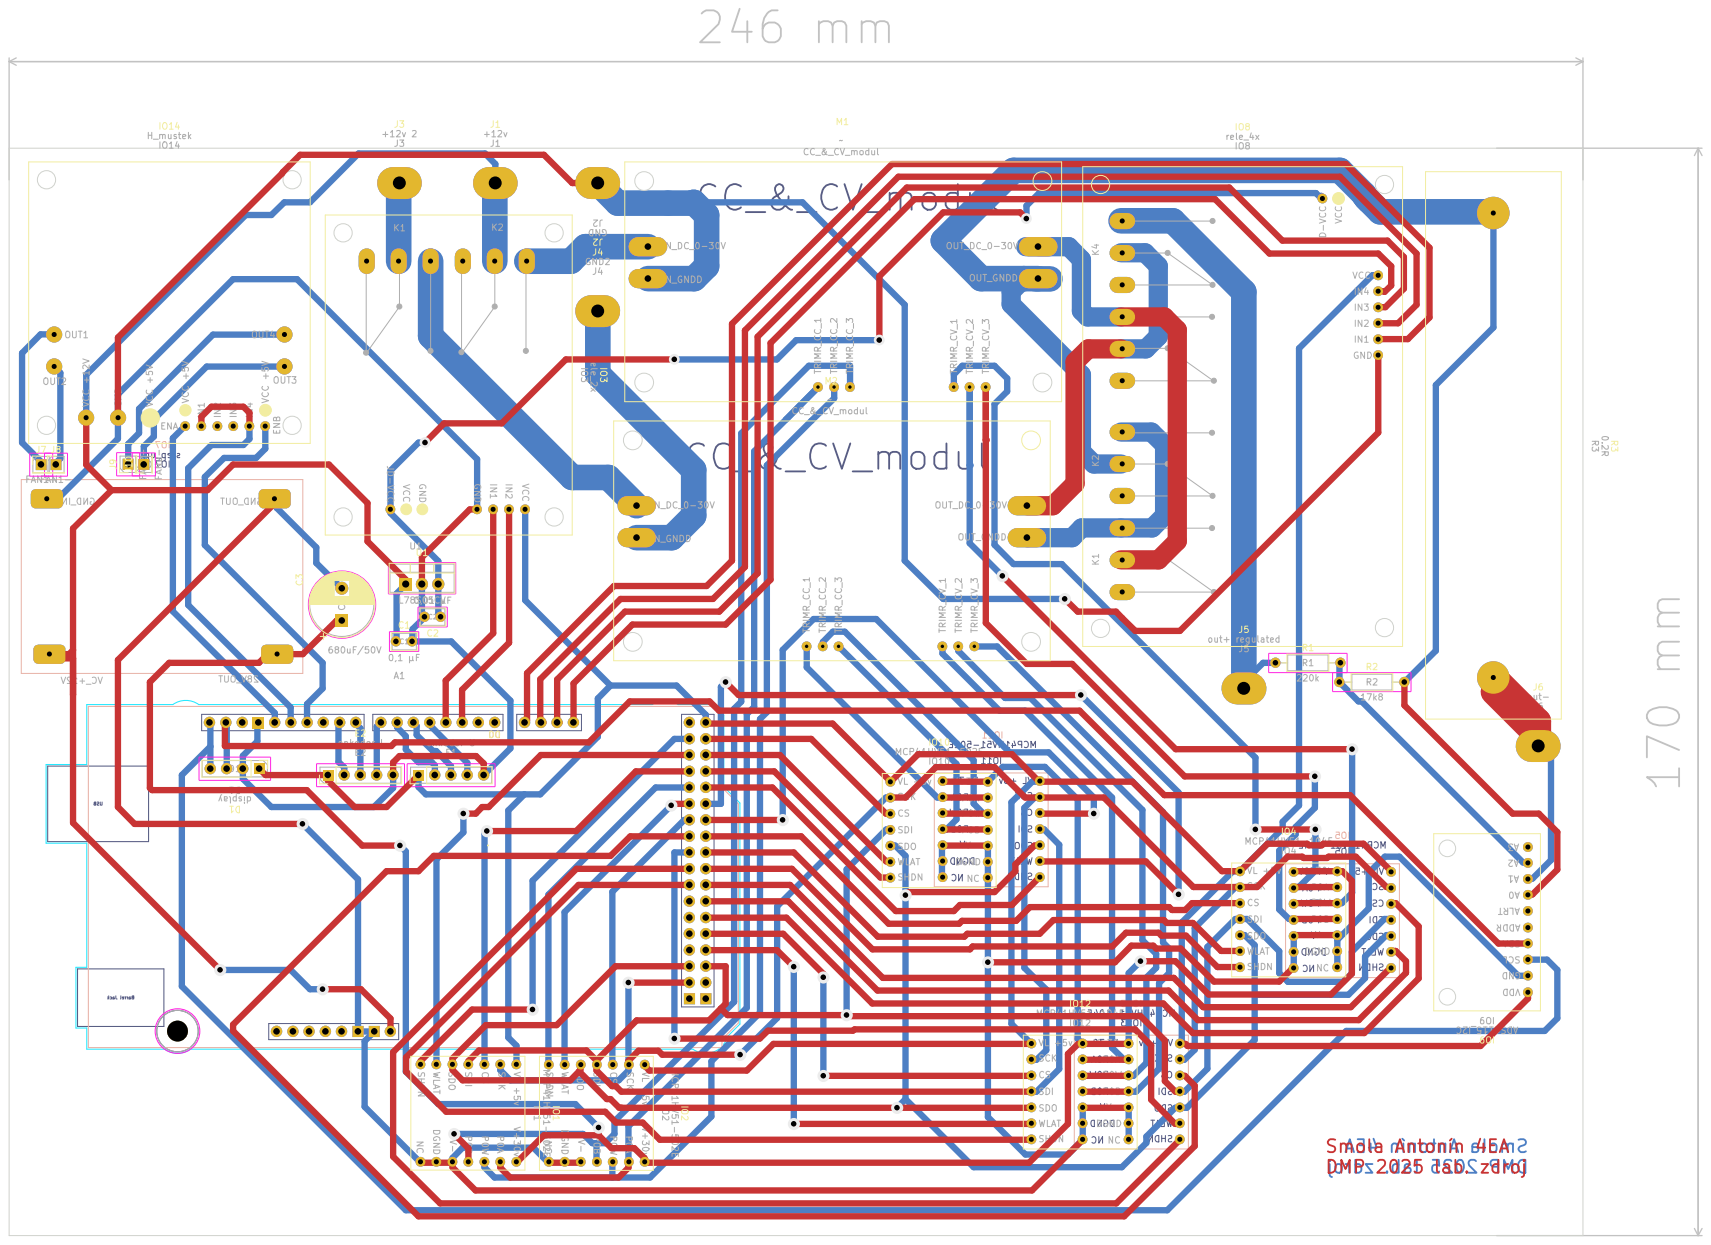
[picture p110: page 1]
