ANToNyS21/DMP2025/smolaan21/mechanika/bottom 1-1 1.5mm bend dim.pdf

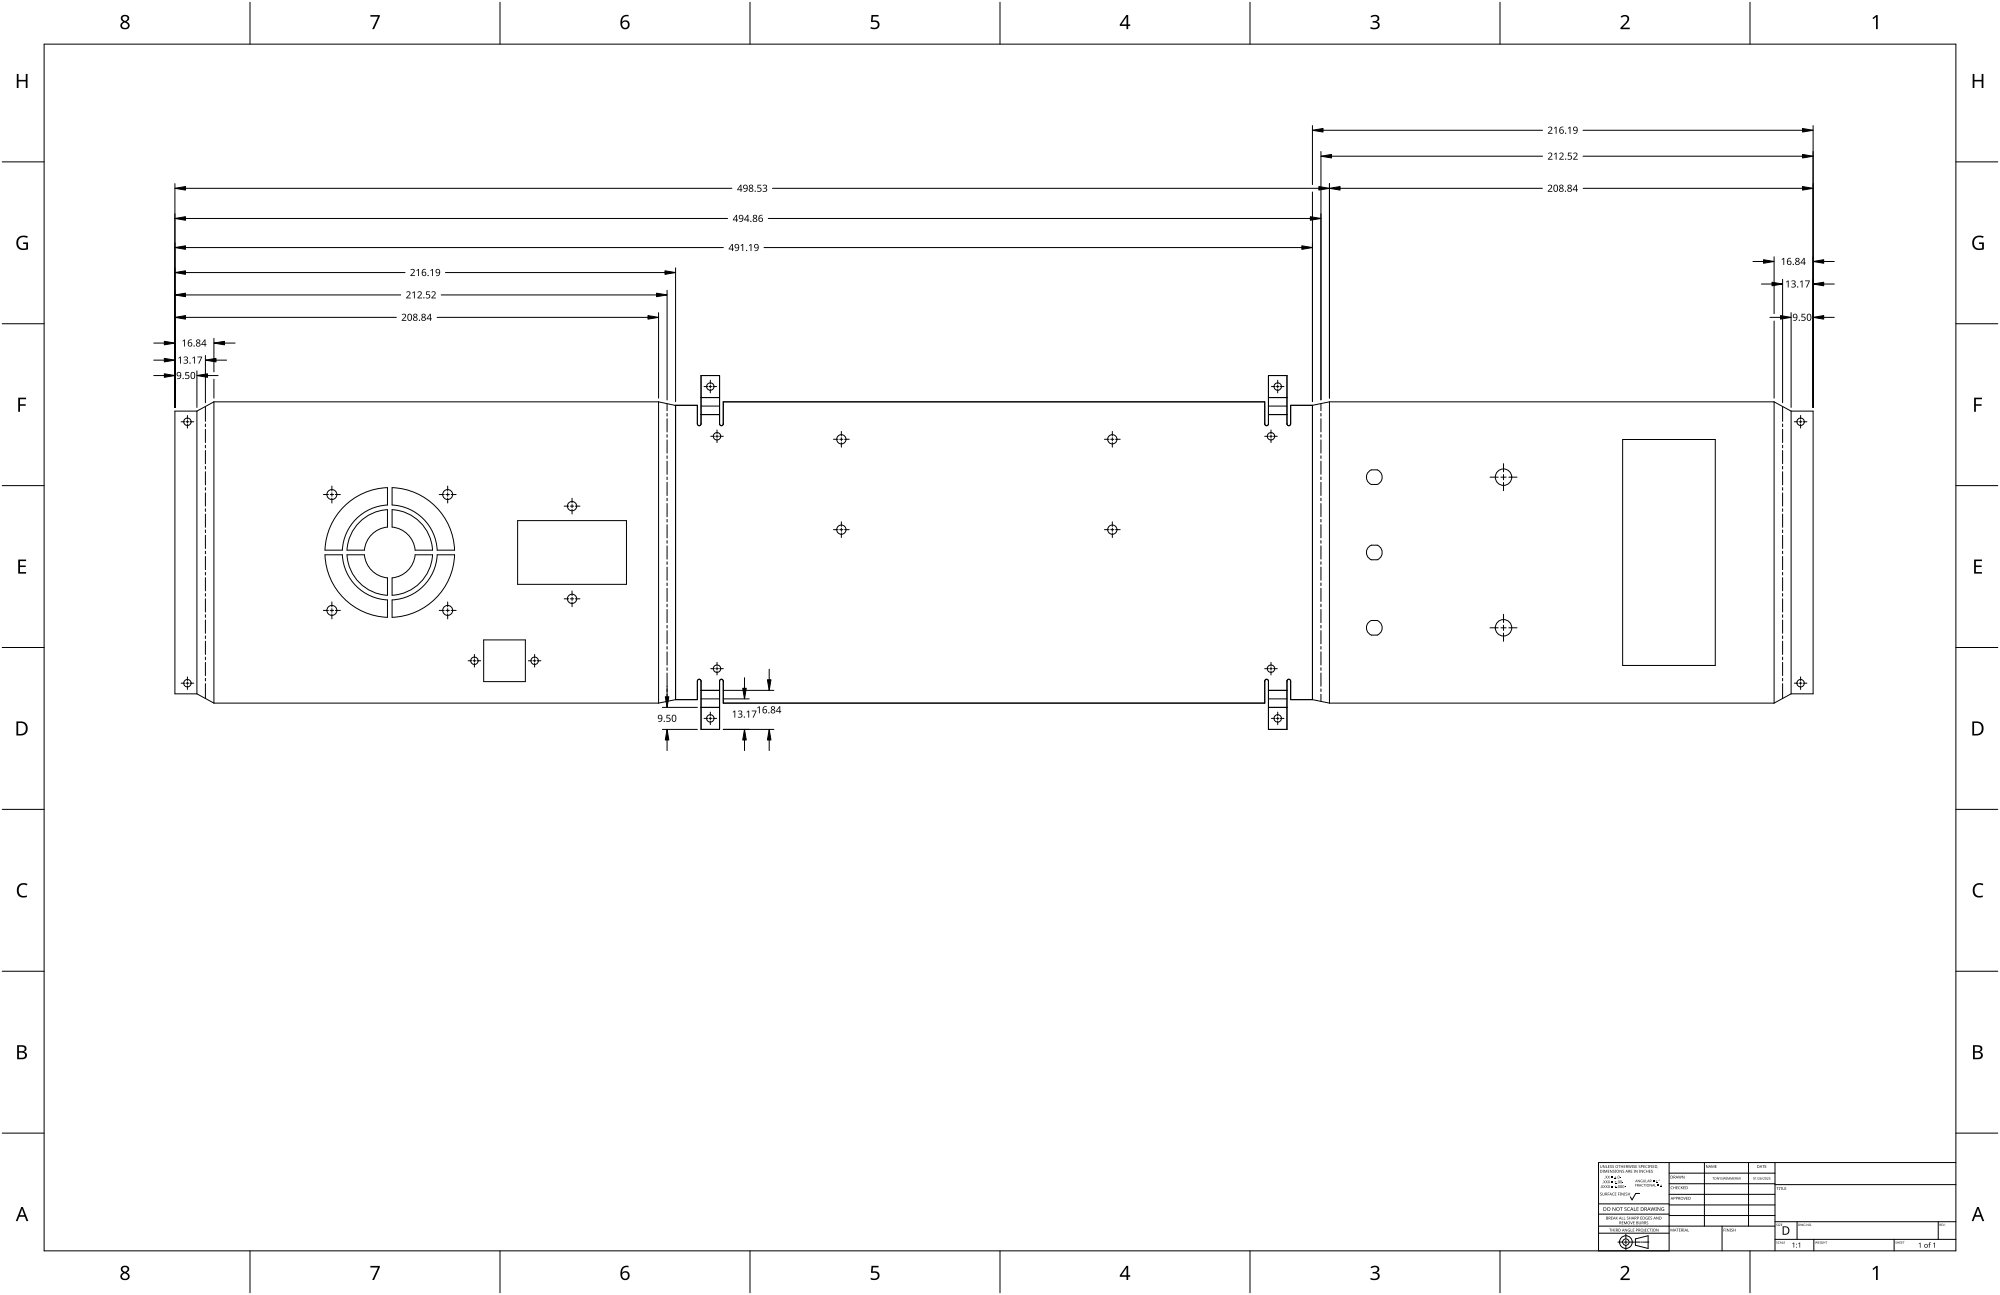
[picture p111: page 1]
