ANToNyS21/DMP2025/smolaan21/mechanika/bottom 1-1 1.5mm.pdf

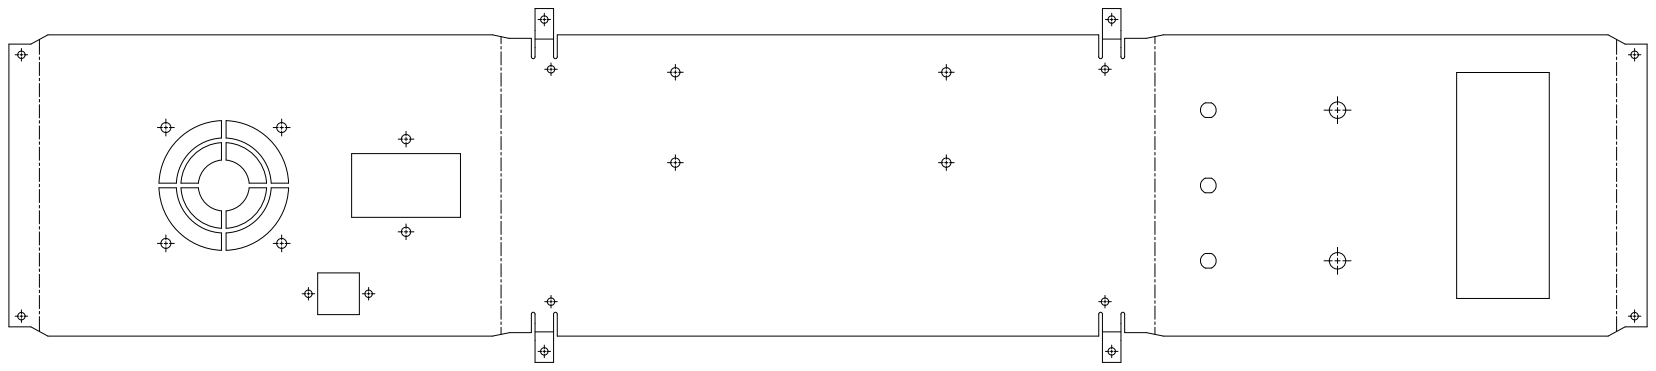
[picture p112: page 1]
