ANToNyS21/DMP2025/smolaan21/mechanika/top 1-1 1.5mm bend dim.pdf

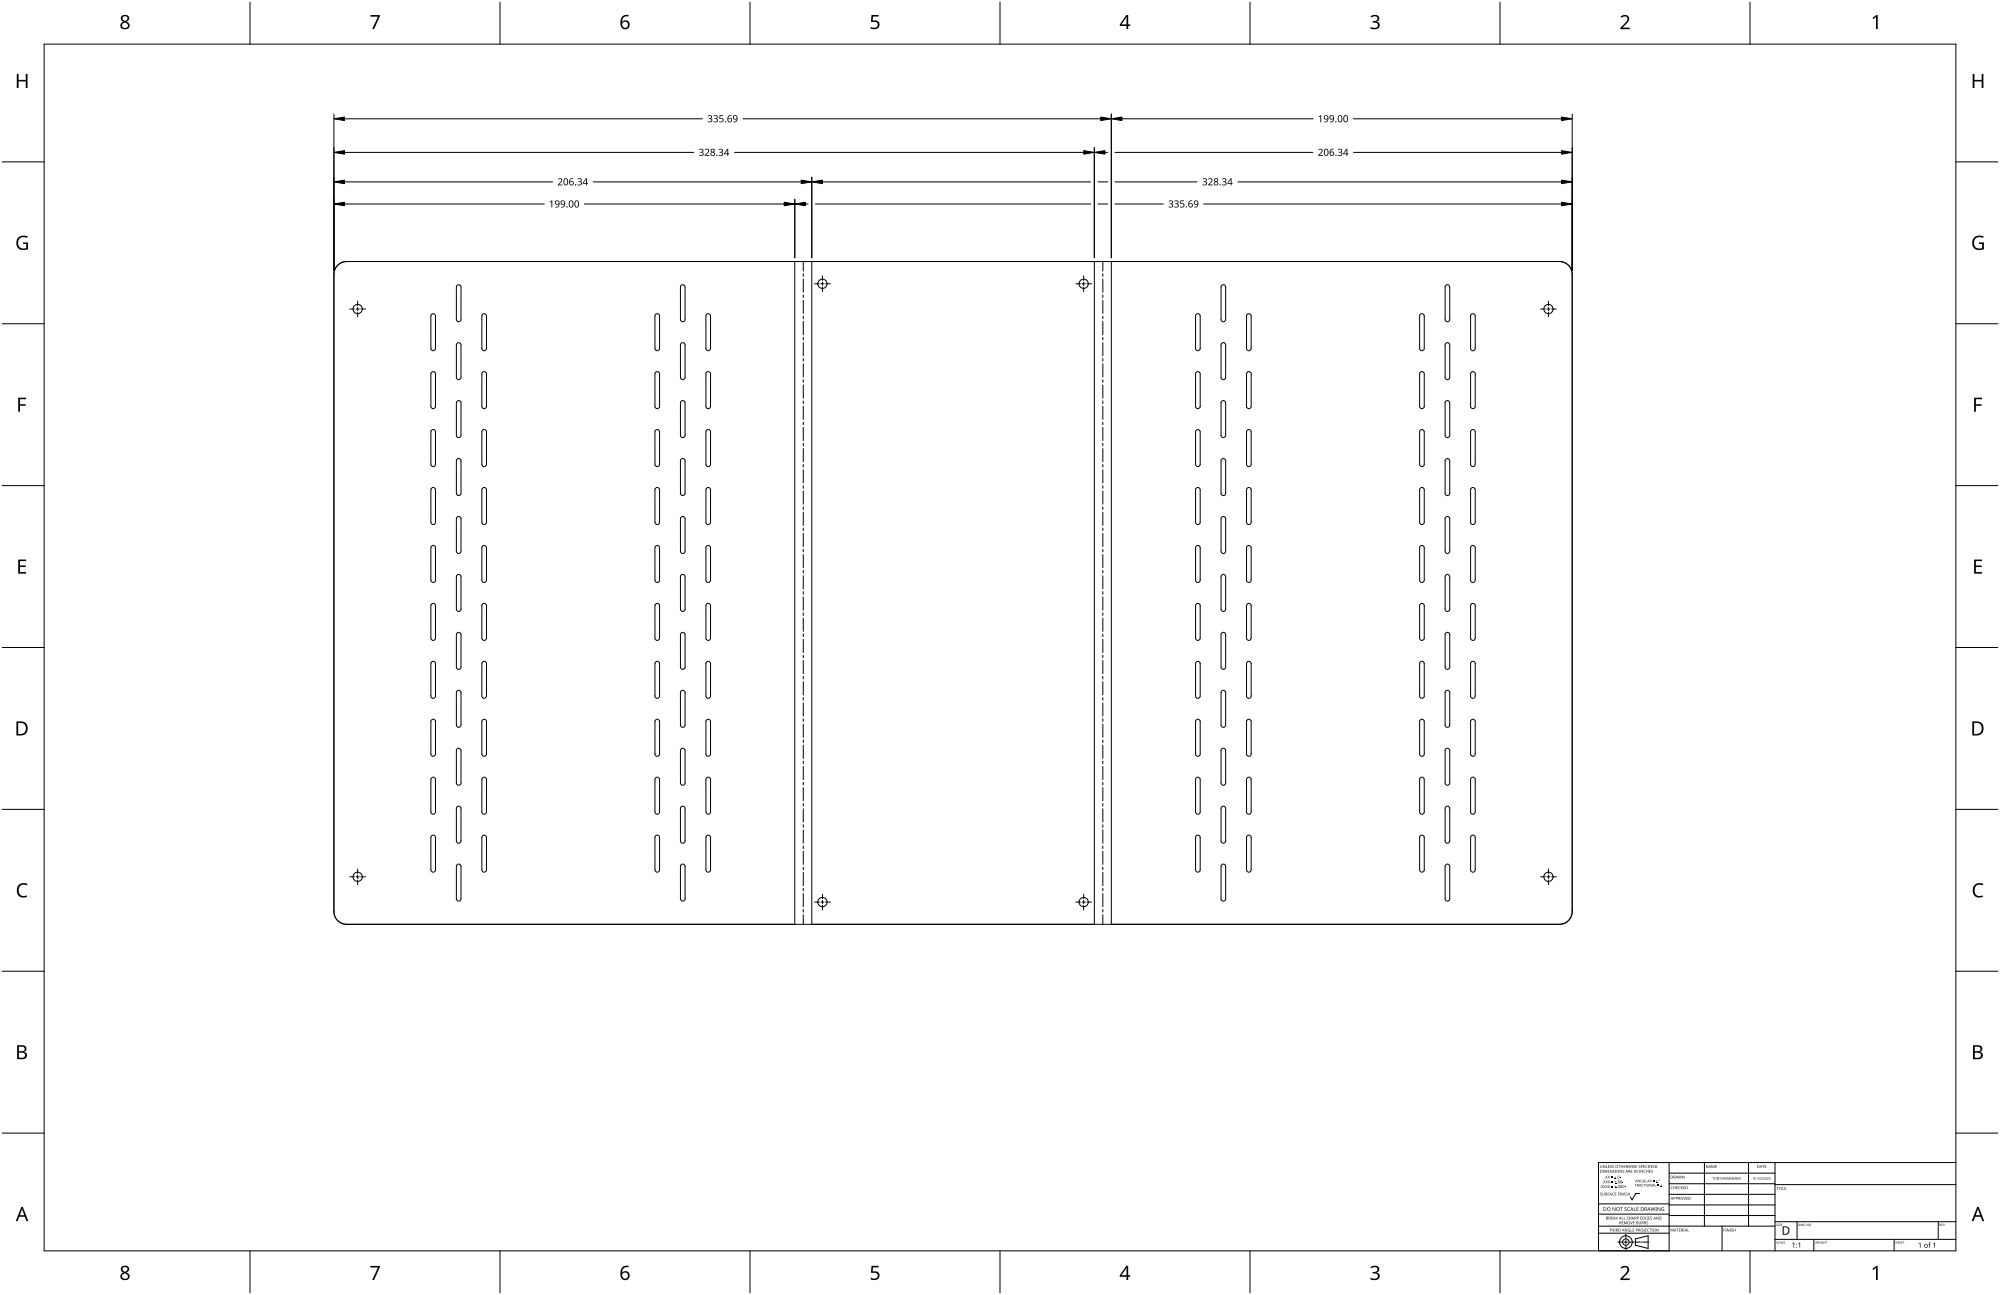
[picture p113: page 1]
