ANToNyS21/DMP2025/smolaan21/mechanika/top 1-1 1.5mm.pdf

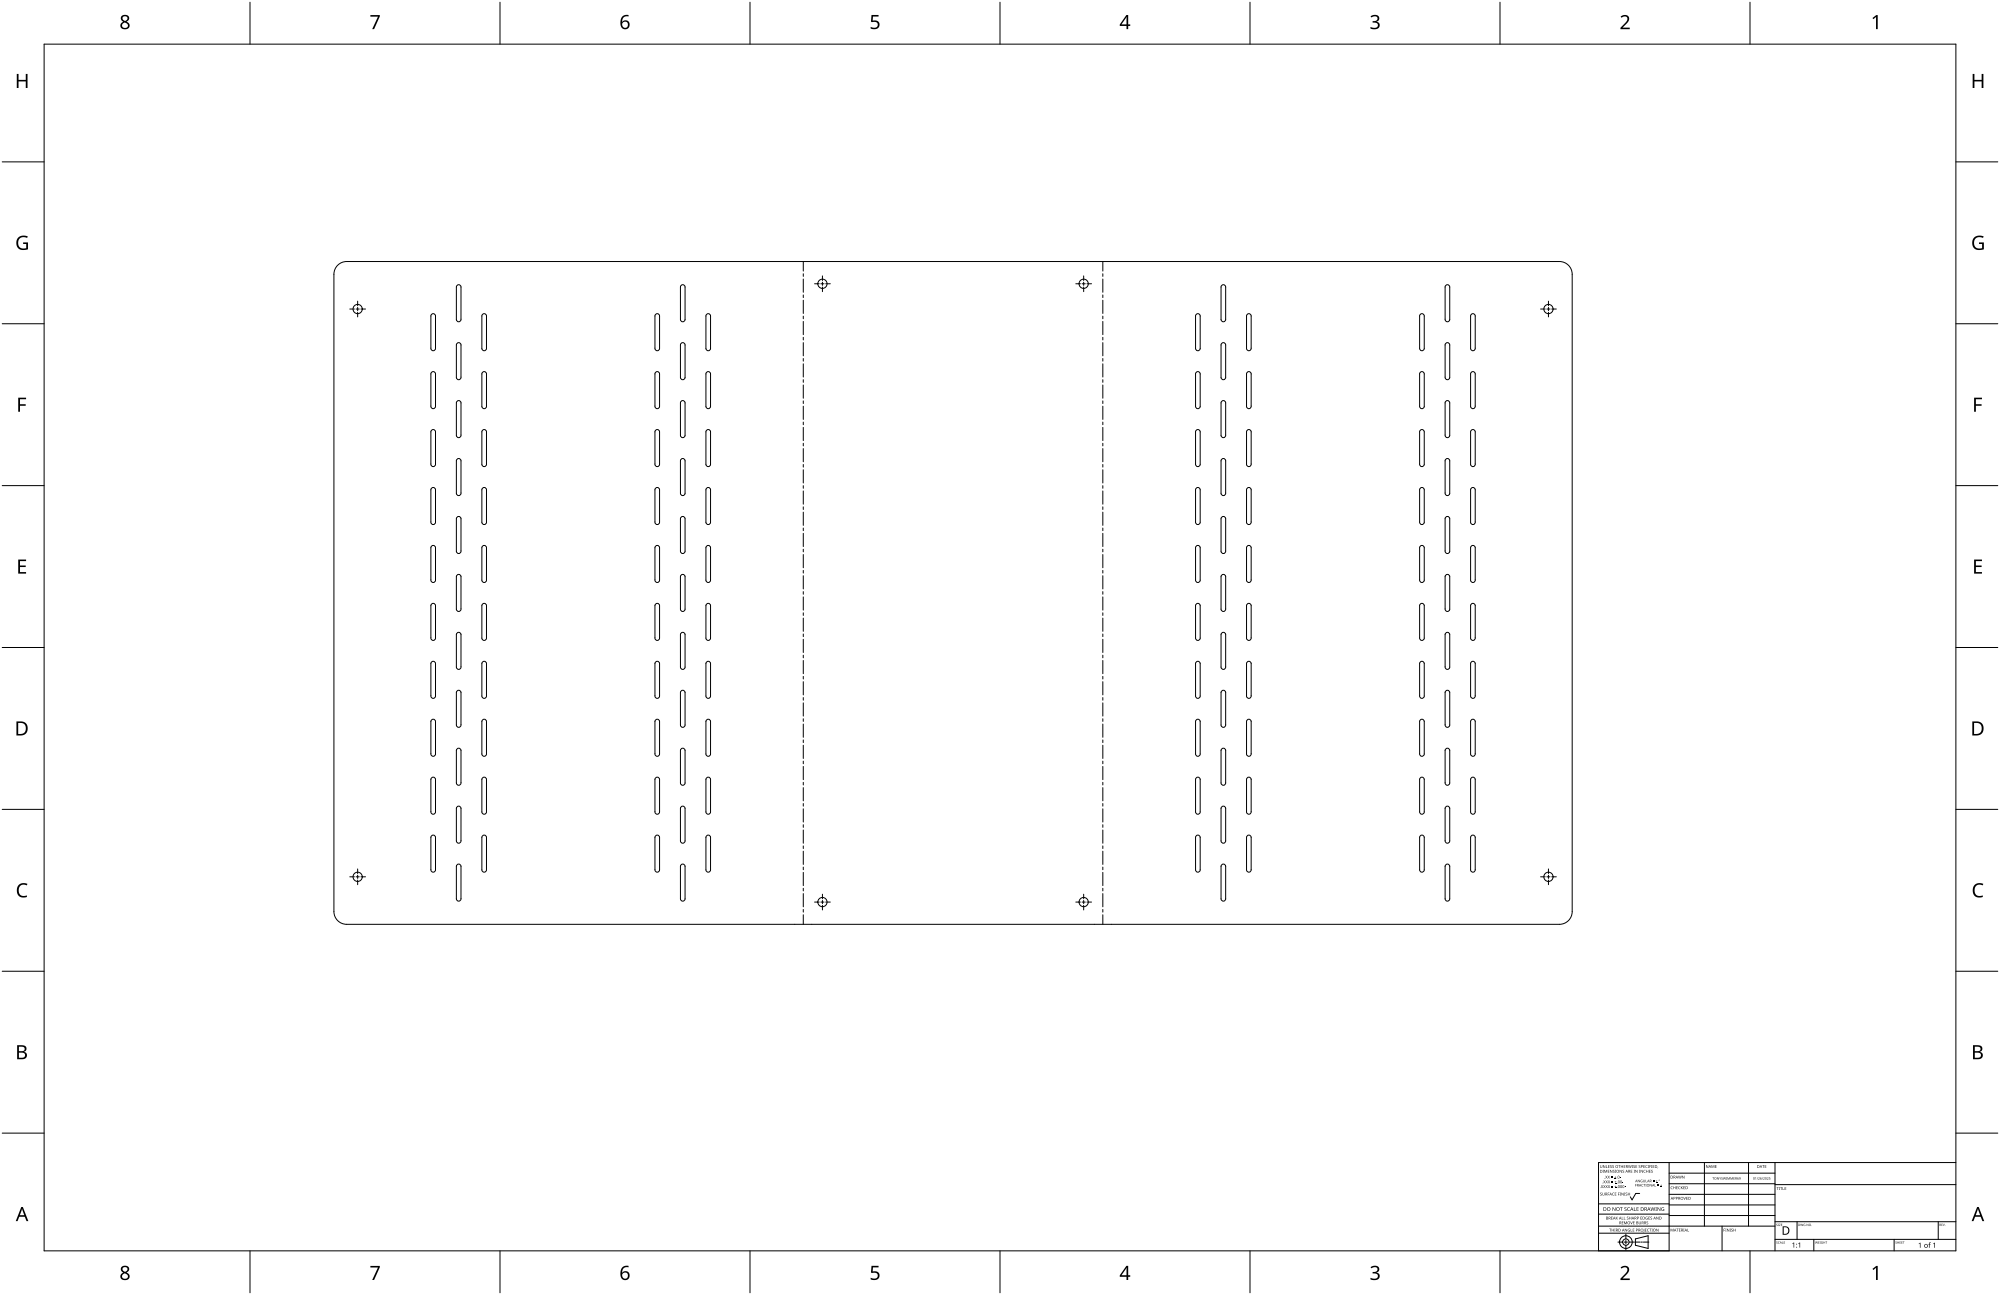
[picture p114: page 1]
