ANToNyS21/DMP2025/schema dmp/eh/schema dmp-F_Cu.pdf

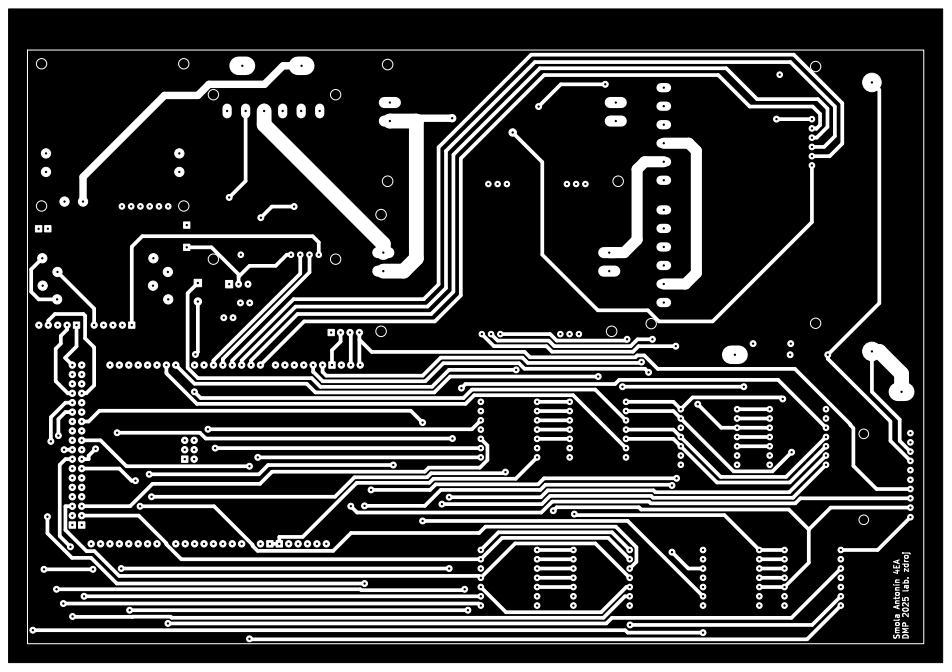
[picture p116: page 1]

Smola þÿAntonín 4EA DMP 2025 lab. zdroj
